LukeB101/Mega-Bit/Design History/Hardware/Prototype Modelling/README.md

Item | Description
--- | --- 
Acrylic 3D Final Prototype | Files for the laser cut case used in the final prototype design 
Production Product | Example injection moulded case for mass production
Prototype 1 8mm LEDs | Laser cut wooden prototype using 8mm LEDs
Prototype 2 10mm LEDs | Second prototype using updated 10mm LEDs
