LukeB101/Mega-Bit/Design History/Hardware/PCB/MEGABIT FINAL PCB/README.md

Revision 1 includes multiple redundant circuits including both HT16K33 and IS31FL3737 drivers.

Revision 2 is the final design for production using the IS31FL3737 and 3.3V buck devices.
