LukeB101/Mega-Bit/Project Management/Gantt Chart.pdf

## mega:bit Project Gantt Chart

Background Research | | | | Legend
Client Meeting | 1st meeting | 2nd meeting | 3rd meeting | General
Primary Research - Survey | | | | Hardware
Decide on Implementation | | | | Software
PCB Design | 1st revision | 2nd revision | 3rd revision | Deliverables
Software Design Method Selection
Supervisor Meeting
Software Implementation
PCB Building and Testing
Leaflet Design
Poster Design
Prototype Building and Testing
Client Demonstration | | 15th June
Deadlines
Leaflet | 9th June
Hackbooth | | 14th June
Documentation/Files | | | 27th June
Peer assessment | | | 27th June

week 6
02/06 - 08/06

week 7
09/06 - 15/06

week 8
16/06 - 22/06

week 9
23/06 - 29/06

week 1
28/04 - 04/05

week 2
05/05 - 11/05

week 3
12/05 - 18/05

week 4
19/05 - 25/05

week 5
26/05 - 1/06
