LukeB101/Mega-Bit/Deliverables/Hackbooth/Poster Illustrations/2nd Revision.png

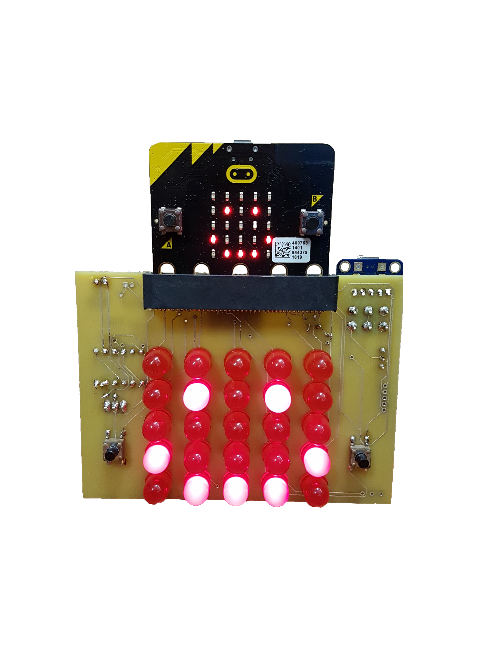
Deliverables/Hackbooth/Poster Illustrations/2nd Revision.png
