LukeB101/Mega-Bit/Deliverables/Hackbooth/Poster Illustrations/Megabit Schematic Diagram.png

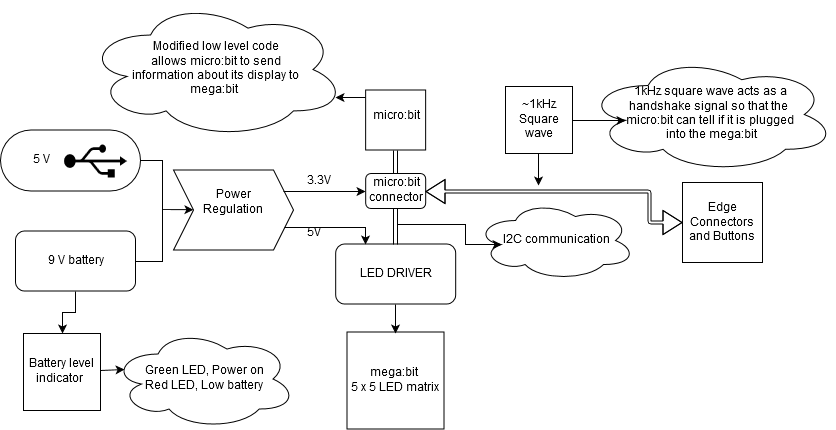
Deliverables/Hackbooth/Poster Illustrations/Megabit Schematic Diagram.png
