LukeB101/Mega-Bit/Deliverables/Leaflet/Leaflet Illustrations/Business Card Back.png

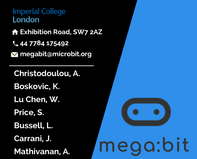
Deliverables/Leaflet/Leaflet Illustrations/Business Card Back.png
