LukeB101/Mega-Bit/Deliverables/Leaflet/Leaflet Illustrations/Business Card Front.png

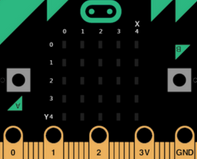
Deliverables/Leaflet/Leaflet Illustrations/Business Card Front.png
