LukeB101/Mega-Bit/Deliverables/Leaflet/Leaflet Illustrations/Megabit (blue).jpg

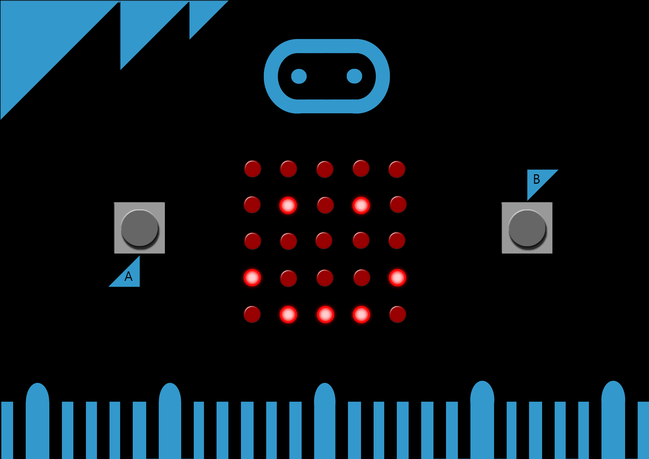
Deliverables/Leaflet/Leaflet Illustrations/Megabit (blue).jpg
