LukeB101/Mega-Bit/Deliverables/Leaflet/Leaflet Illustrations/Megabit Final Design.jpg

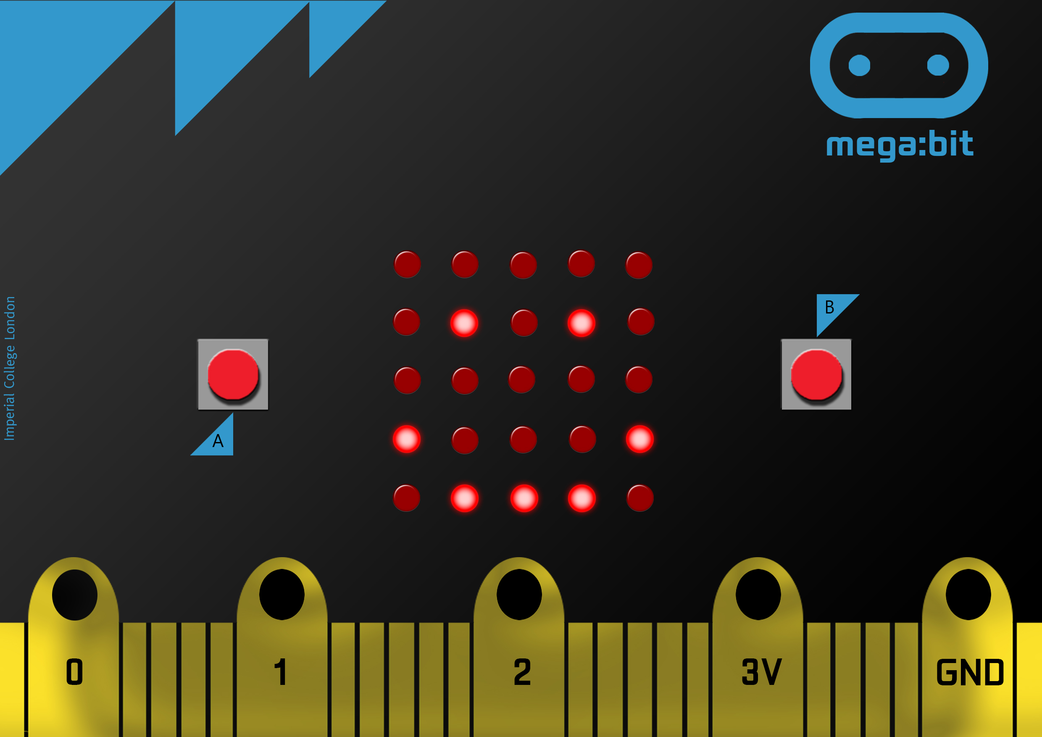
Deliverables/Leaflet/Leaflet Illustrations/Megabit Final Design.jpg
