LukeB101/Mega-Bit/Deliverables/Leaflet/Leaflet Illustrations/Megabit with Slot.jpg

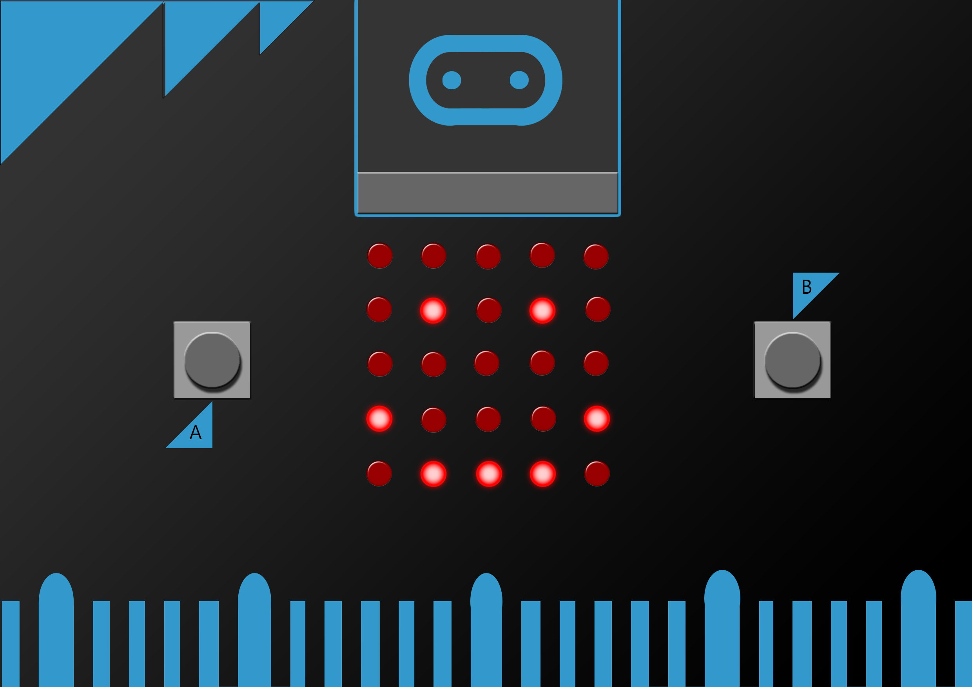
Deliverables/Leaflet/Leaflet Illustrations/Megabit with Slot.jpg
