LukeB101/Mega-Bit/Deliverables/Leaflet/Leaflet Illustrations/Piechart.png

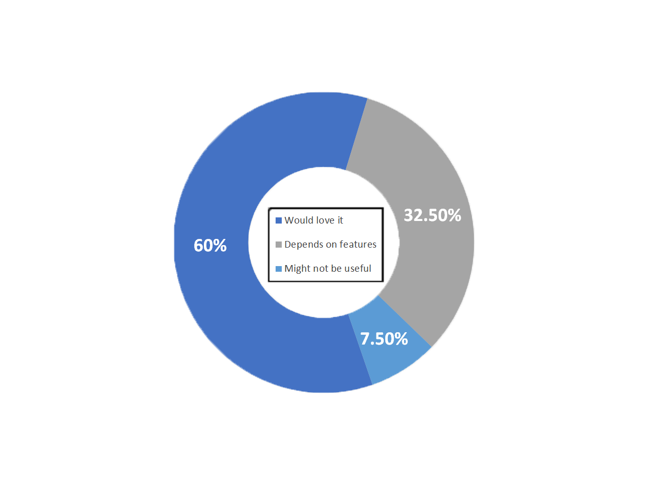
Deliverables/Leaflet/Leaflet Illustrations/Piechart.png
