LukeB101/Mega-Bit/Design History/Hardware/Prototype Modelling/Production Product/Final Design/render of case with PCB.PNG

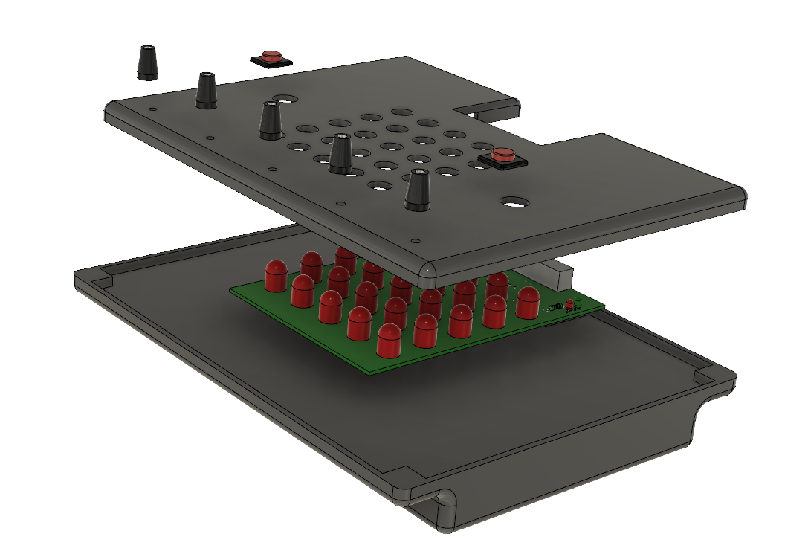
Design History/Hardware/Prototype Modelling/Production Product/Final Design/render of case with PCB.PNG
