LukeB101/Mega-Bit/Design History/Hardware/Prototype Modelling/Production Product/Final Design/render of MegaBit.PNG

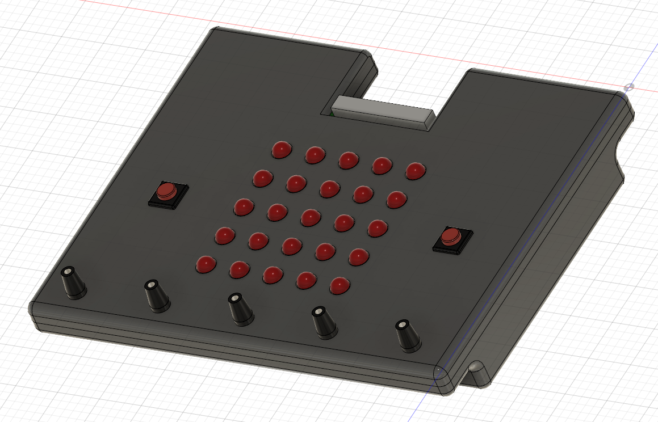
Design History/Hardware/Prototype Modelling/Production Product/Final Design/render of MegaBit.PNG
