LukeB101/Mega-Bit/Design History/Hardware/Prototype Modelling/Production Product/Production Quote Files/back.PNG

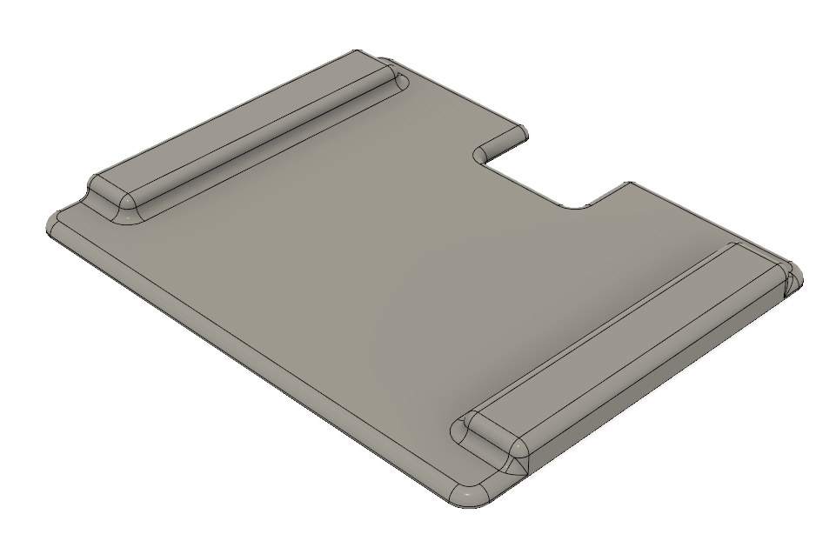
Design History/Hardware/Prototype Modelling/Production Product/Production Quote Files/back.PNG
