LukeB101/Mega-Bit/Design History/Hardware/Prototype Modelling/Prototype 1 8mm LEDs/8mm LED MegaBit.png

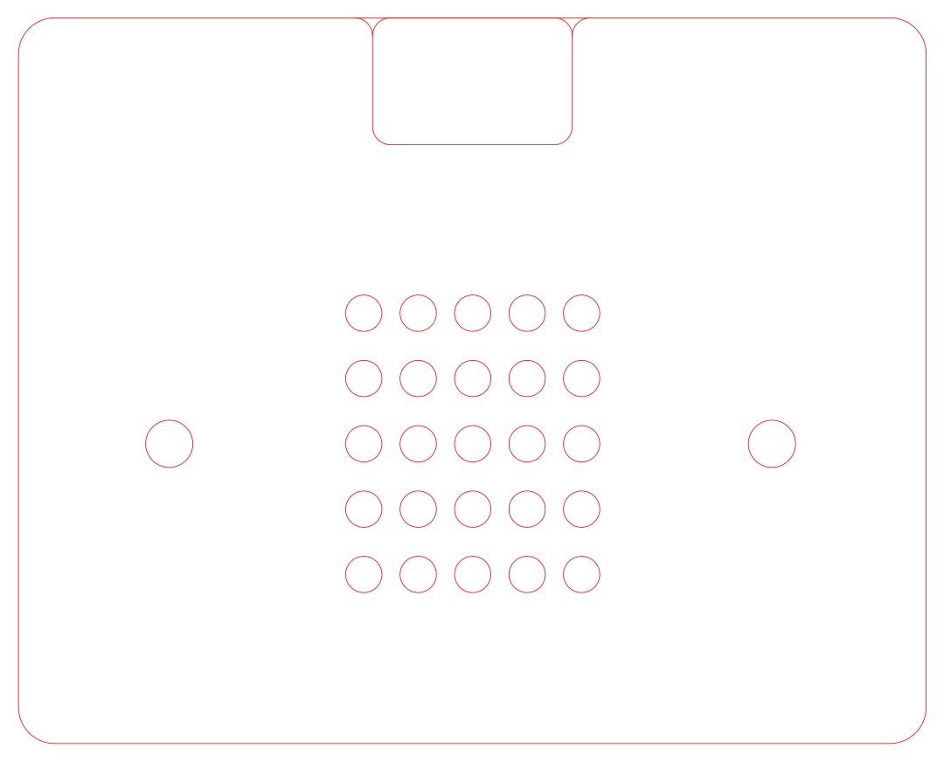
Design History/Hardware/Prototype Modelling/Prototype 1 8mm LEDs/8mm LED MegaBit.png
