LukeB101/Mega-Bit/Design History/Hardware/Prototype Modelling/Prototype 2 10mm LEDs/10mm LED MegaBit.png

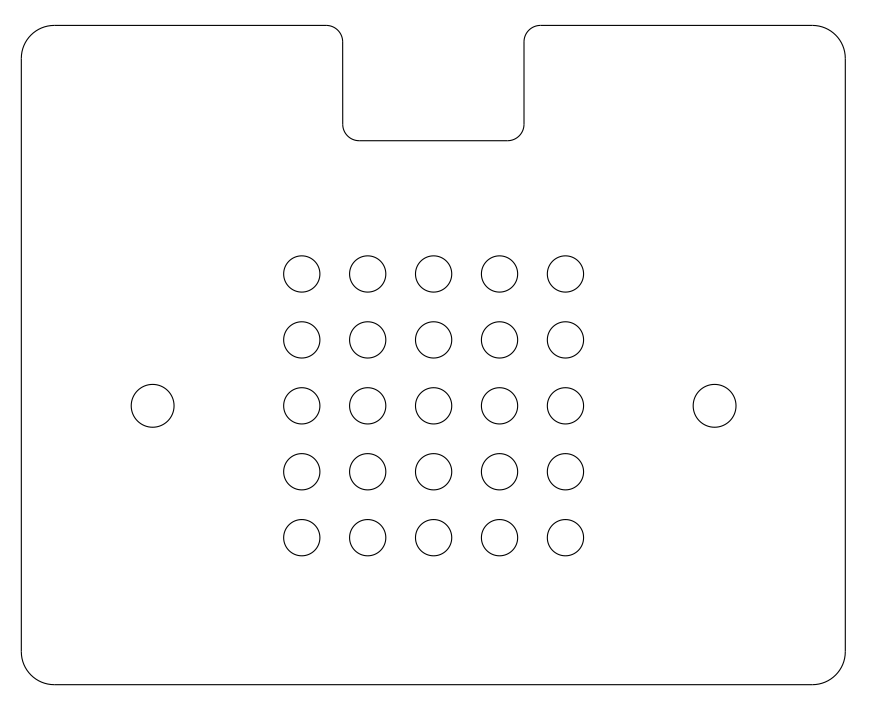
Design History/Hardware/Prototype Modelling/Prototype 2 10mm LEDs/10mm LED MegaBit.png
