LukeB101/Mega-Bit/Design History/Hardware/Prototype Modelling/Prototype 2 10mm LEDs/front dimensions.PNG

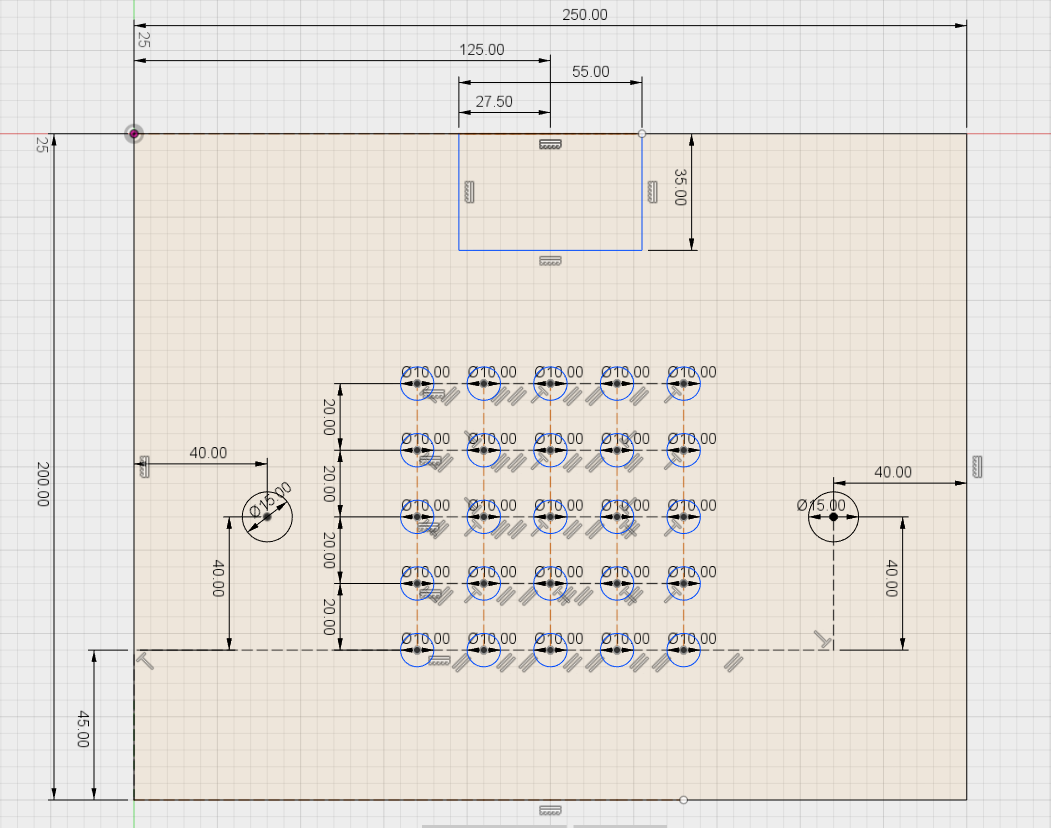
Design History/Hardware/Prototype Modelling/Prototype 2 10mm LEDs/front dimensions.PNG
