LukeB101/Mega-Bit/Final Product Design/CAD Files/back.PNG

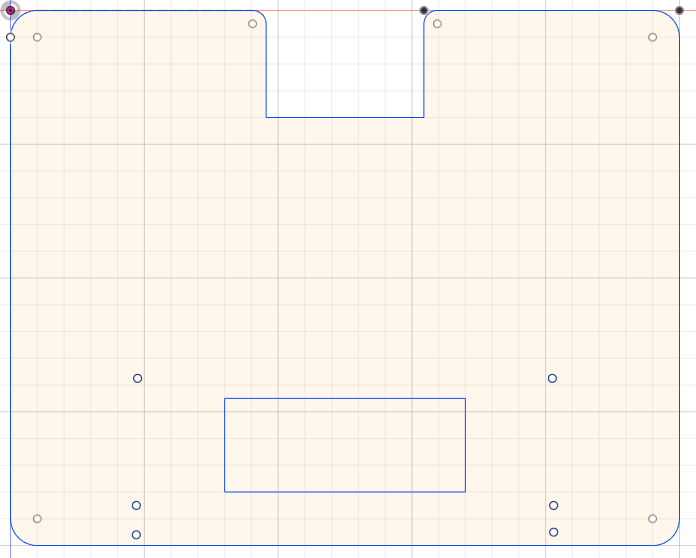
Final Product Design/CAD Files/back.PNG
