LukeB101/Mega-Bit/Final Product Design/CAD Files/front acrylic cover.PNG

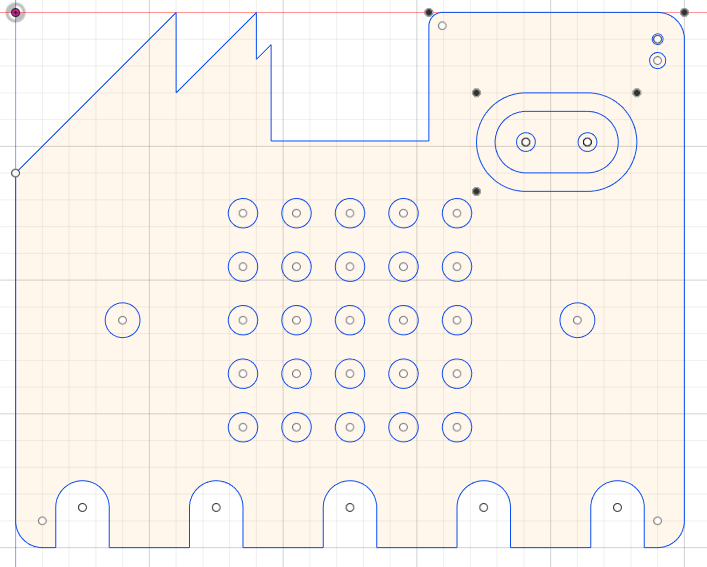
Final Product Design/CAD Files/front acrylic cover.PNG
