LukeB101/Mega-Bit/Final Product Design/CAD Files/front painted layer.PNG

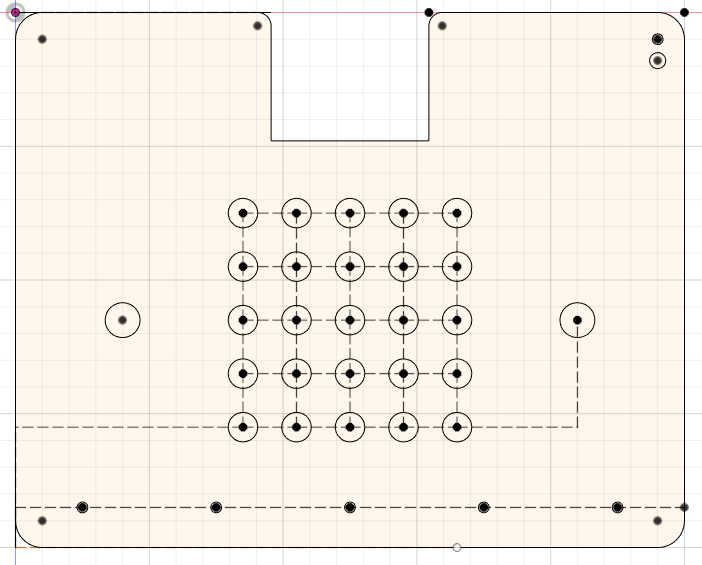
Final Product Design/CAD Files/front painted layer.PNG
