LukeB101/Mega-Bit/Final Product Design/CAD Files/sides.PNG

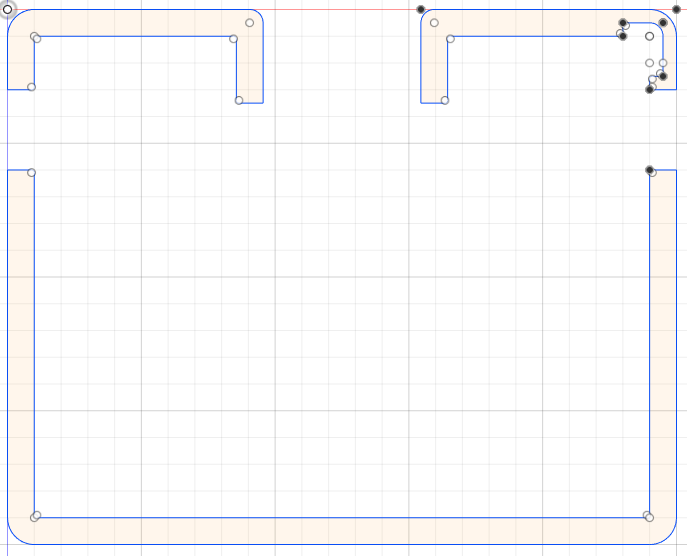
Final Product Design/CAD Files/sides.PNG
