LukeB101/Mega-Bit/Final Product Design/CAD Files/stand.PNG

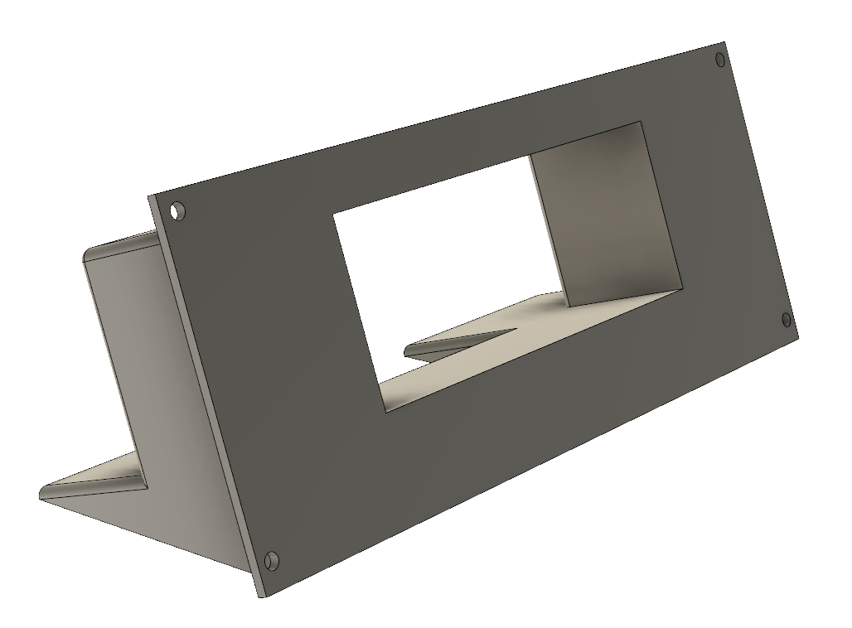
Final Product Design/CAD Files/stand.PNG
