LukeB101/Mega-Bit/pictures/Final prototype back view.jpg

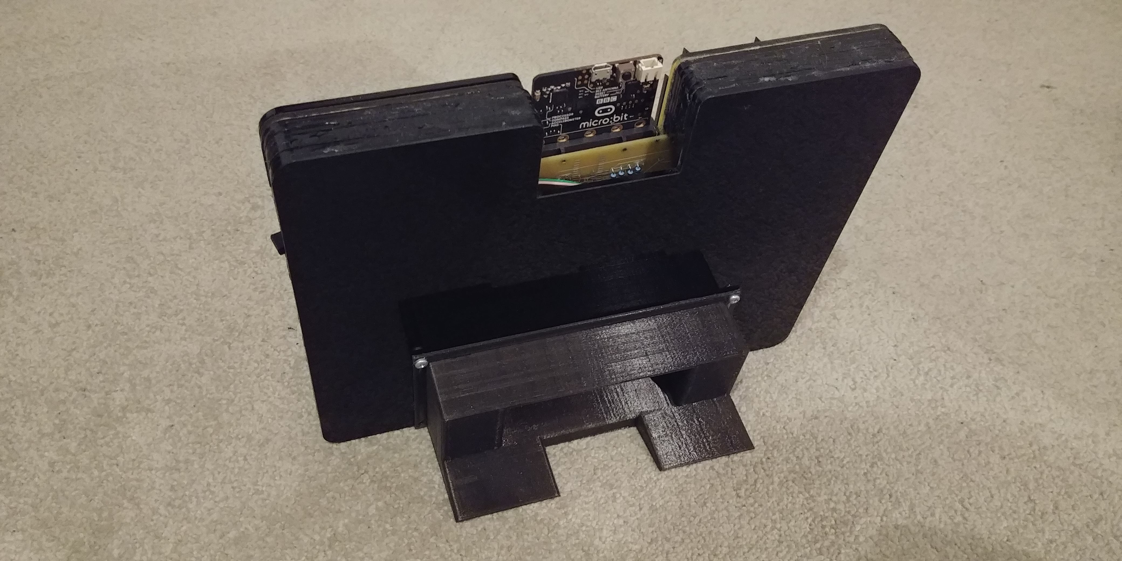
pictures/Final prototype back view.jpg
