LukeB101/Mega-Bit/pictures/Final prototype front view.jpg

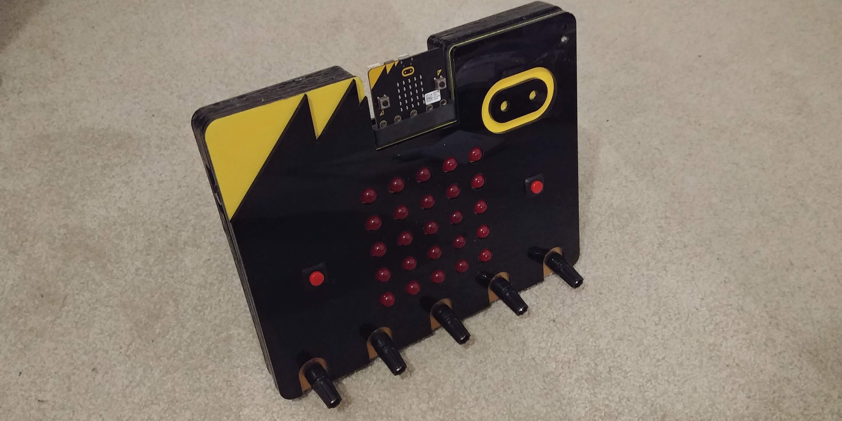
pictures/Final prototype front view.jpg
