LukeB101/Mega-Bit/Design History/Manufacturing/Plastic Case Supplier Quotes/Plastic Mold Quote - China Plastic.pdf

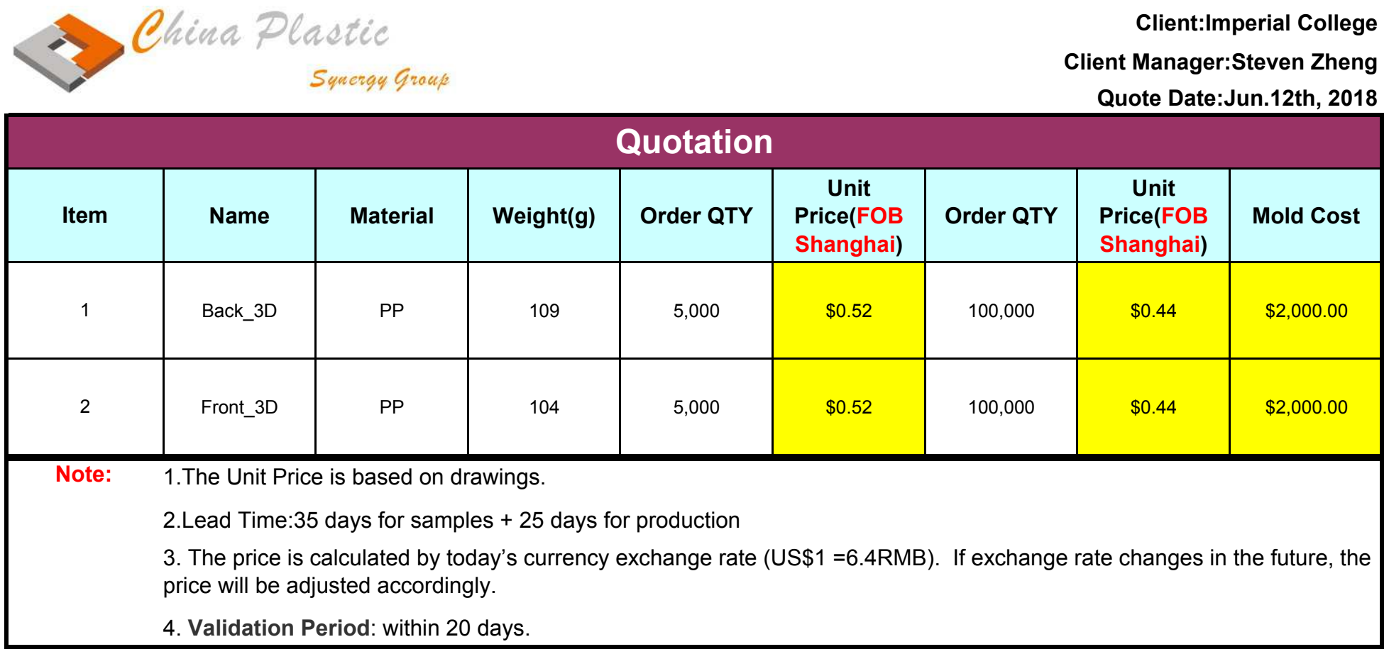
[picture p42: figure]
Client:Imperial College; Client Manager:Steven Zheng; Quote Date:Jun.12th, 2018; Item; Name; Material; Weight(g); Order QTY; Unit Price(FOB Shanghai); Mold Cost; Back_3D; Front_3D; Note:; 4. Validation Period: within 20 days.; 1.The Unit Price is based on drawings.; Quotation; price will be adjusted accordingly.

2.Lead Time:35 days for samples + 25 days for production
3. The price is calculated by today’s currency exchange rate (US$1 =6.4RMB). If exchange rate changes in the future, the
