LukeB101/Mega-Bit/Design History/Components/Microbit Breakout Board/Supplier Order.JPG

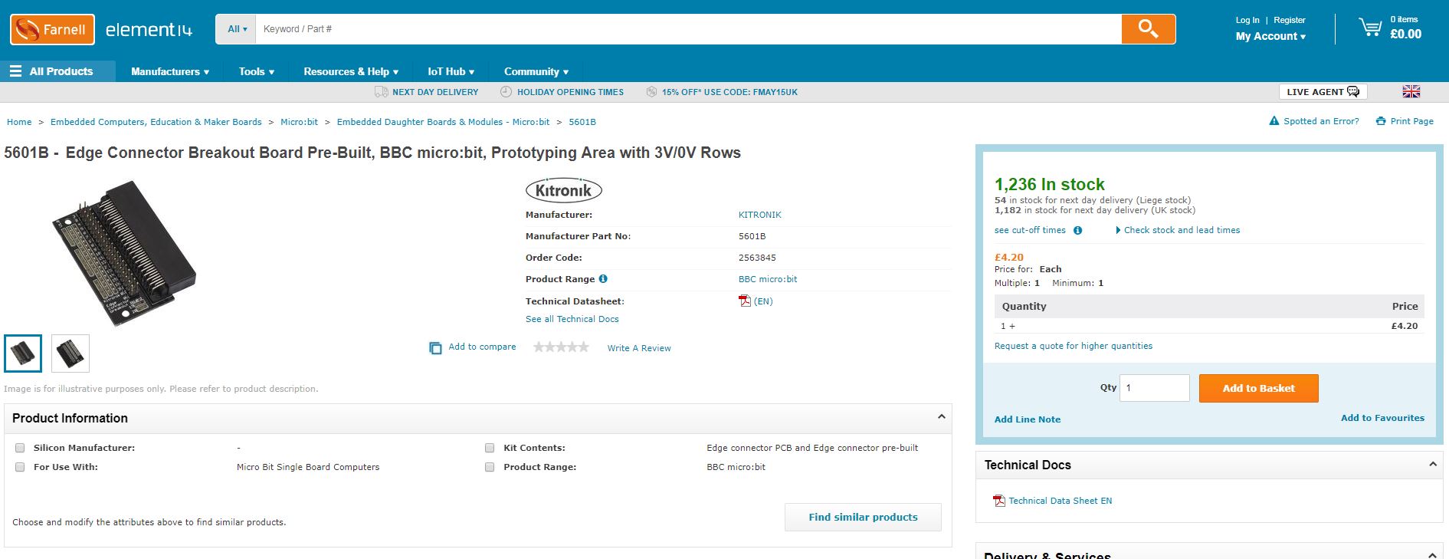
Design History/Components/Microbit Breakout Board/Supplier Order.JPG
