LukeB101/Mega-Bit/Design History/End Product Testing/Pictures/3V3 + 5V.png

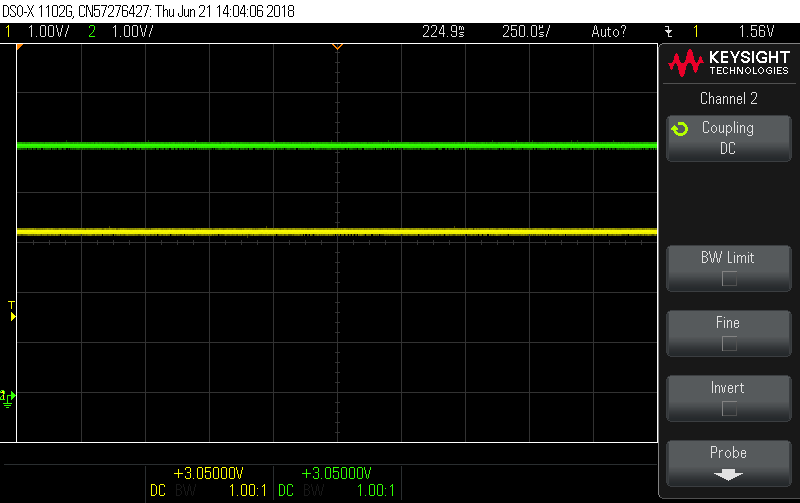
Design History/End Product Testing/Pictures/3V3 + 5V.png
