LukeB101/Mega-Bit/Design History/End Product Testing/Pictures/Distance test.jpg

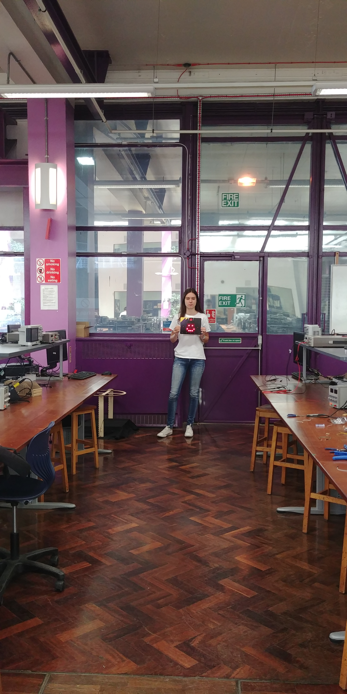
Design History/End Product Testing/Pictures/Distance test.jpg
