LukeB101/Mega-Bit/Design History/End Product Testing/Pictures/I2C example.png

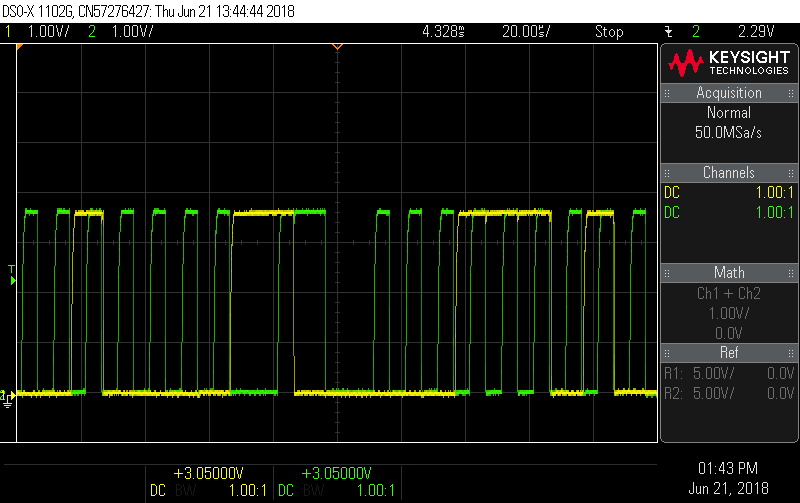
Design History/End Product Testing/Pictures/I2C example.png
