LukeB101/Mega-Bit/Design History/End Product Testing/Pictures/Single TX.png

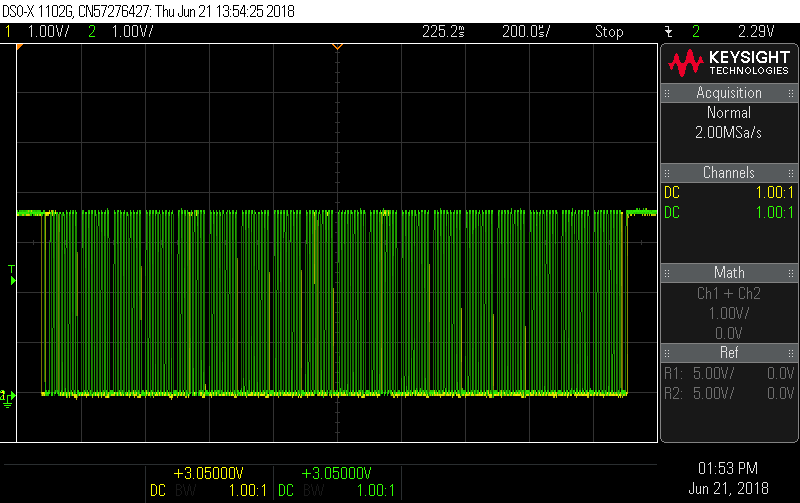
Design History/End Product Testing/Pictures/Single TX.png
