LukeB101/Mega-Bit/Design History/End Product Testing/Pictures/Startup Comms.png

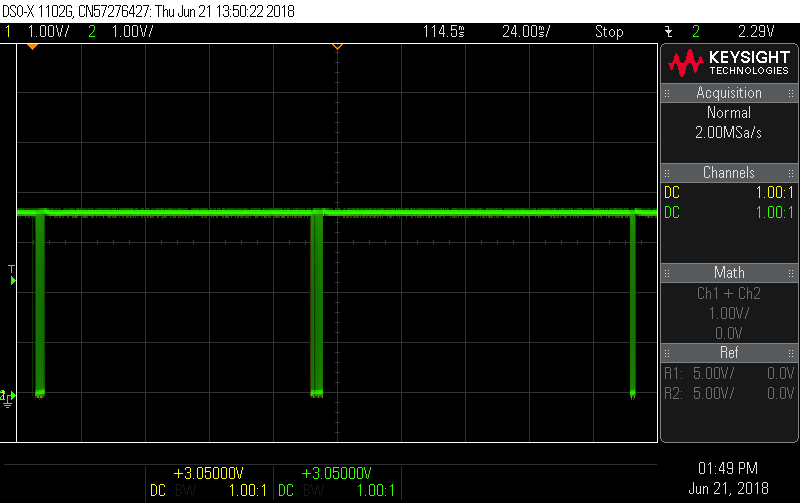
Design History/End Product Testing/Pictures/Startup Comms.png
