LukeB101/Mega-Bit/Final Product Design/PCB/rev2 (incomplete)/MEGABIT.PDF

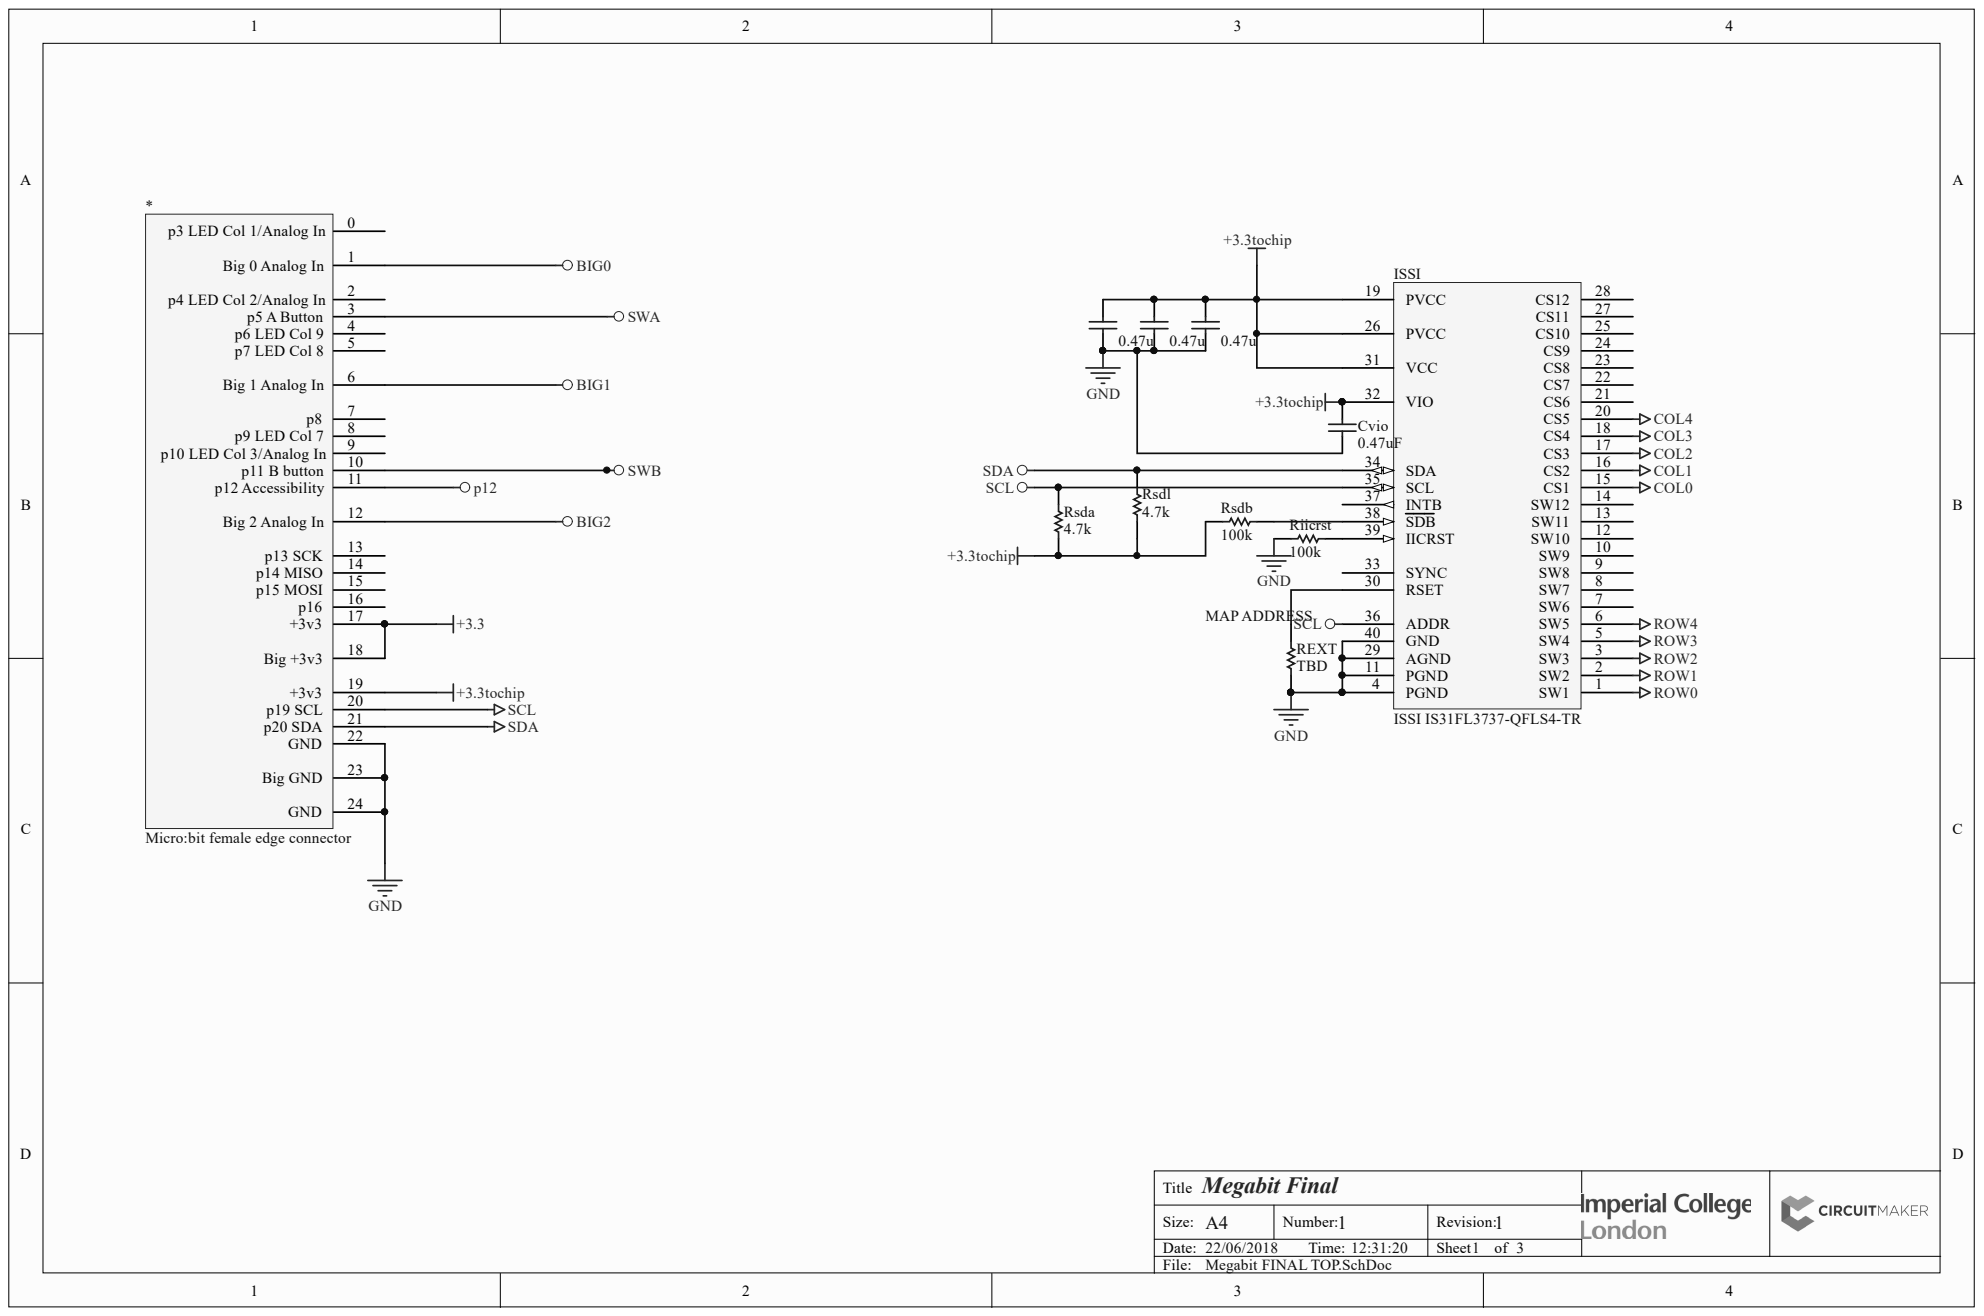
[picture p93: page 1]
t FIN; 1 PGND; ISSI IS3; 3 SCK 4 MISO 5 MOSI; 9 SCL 0 SD; t female ed; PIRsdb02 PIRsdl02; PIRiicrst01 PIISSI039; PIISSI034 PIRsdl01

T i t l e Mega bit Fina l

Size: A4 | N umber: 1 | Rev i s i o n : 1
Date: / / T ime: : : | | Sheet o f


Title Megabit LED Matrix

Size: A4 | Number: 2 | Revision: 1
22/06/2018 Time: 12:31:20 | | Sheet of

tery i; PIU103; PIDlow02 PIU101

T i t l e Mega bit Battery Indicato r

Size: A4 | N umber: 3 | Rev i s i o n : 1

/ / T ime: : : | | Sheet o f

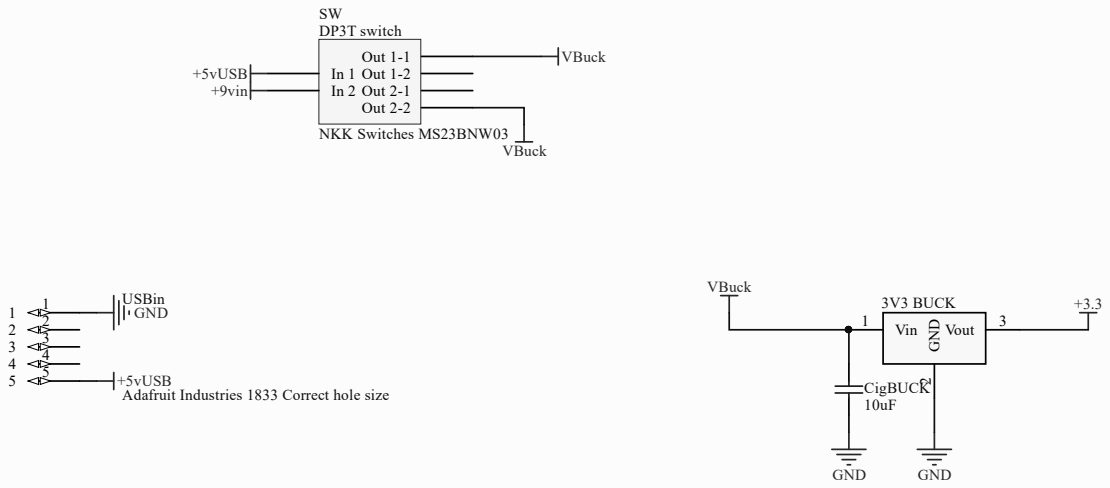
[picture p94: page 4]
Vin 1; GND 2 Vout 3; 3V3 BUCK; Out 1-1 Out 1-2 Out 2-1; DP3T switch; Out 2-2; NKK Switches MS23BNW03; PI3V3 BUCK01; PI3V3 BUCK02; PI3V3 BUCK03; CO3V3 BUCK; PICigBUCK02 COCigBUCK

+5vUSB
Adafruit Industries 1833 Correct hole size

Title Megabit Final Power

Size: A4 | Number: 4 | Revision: 1

TRIG 2; RST 4; THR 6; GND; Res1 C555

f= 1/(1.4RC), datasheet reccomends minimal C and large R

Title Megabit Final Handshake Circuitry

Size: A4 | Number: 5 | Revision: 1
