LukeB101/Mega-Bit/Design History/Hardware/PCB/PCB 3rd revision/MEGABIT.PDF

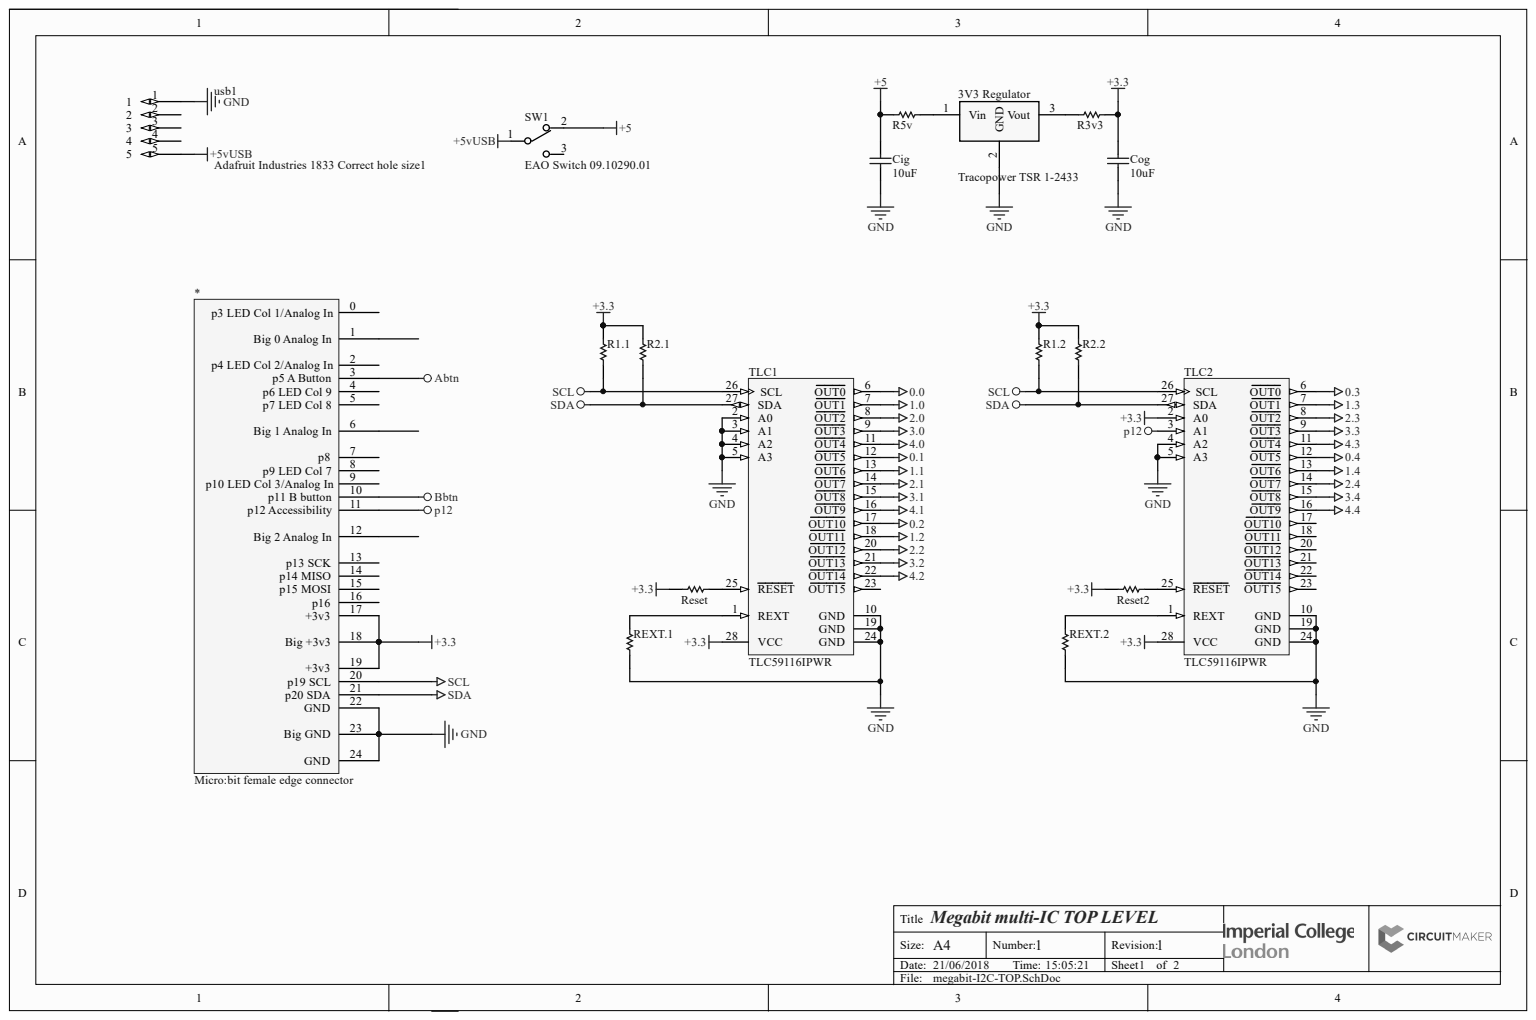
[picture p95: page 1]
EAO Switch 09.10290.01; REXT 1; RESET 25; SCL 26 SDA 27; VCC 28; 4.4 GND; GND; Reset2 +3.3; +3.3 Reset; p3 LED Col 1/Analog In; Big 0 Analog In; p4 LED Col 2/Analog In; p5 A Button; p6 LED Col 9; p7 LED Col 8; Big 1 Analog In; p9 LED Col 7; p10 LED Col 3/Analog In; p11 B button; p12 Accessibility; Big 2 Analog In; p13 SCK; p14 MISO; p15 MOSI; Big +3v3; p19 SCL; p20 SDA; Big GND; Vin 1; GND 2 Vout 3; 3V3 Regulator; Tracopower TSR 1-2433

+5vUSB
Adafruit Industries 1833 Correct hole size1

Micro:bit female edge connector

Title Megabit multi-IC TOP LEVEL

Size: A4 | Number: 1 | Revision: 1
Date: 21/06/2018 Time: 15:05:21 | | Sheet 1 of 2

megabit-I2C-TOP.SchDoc

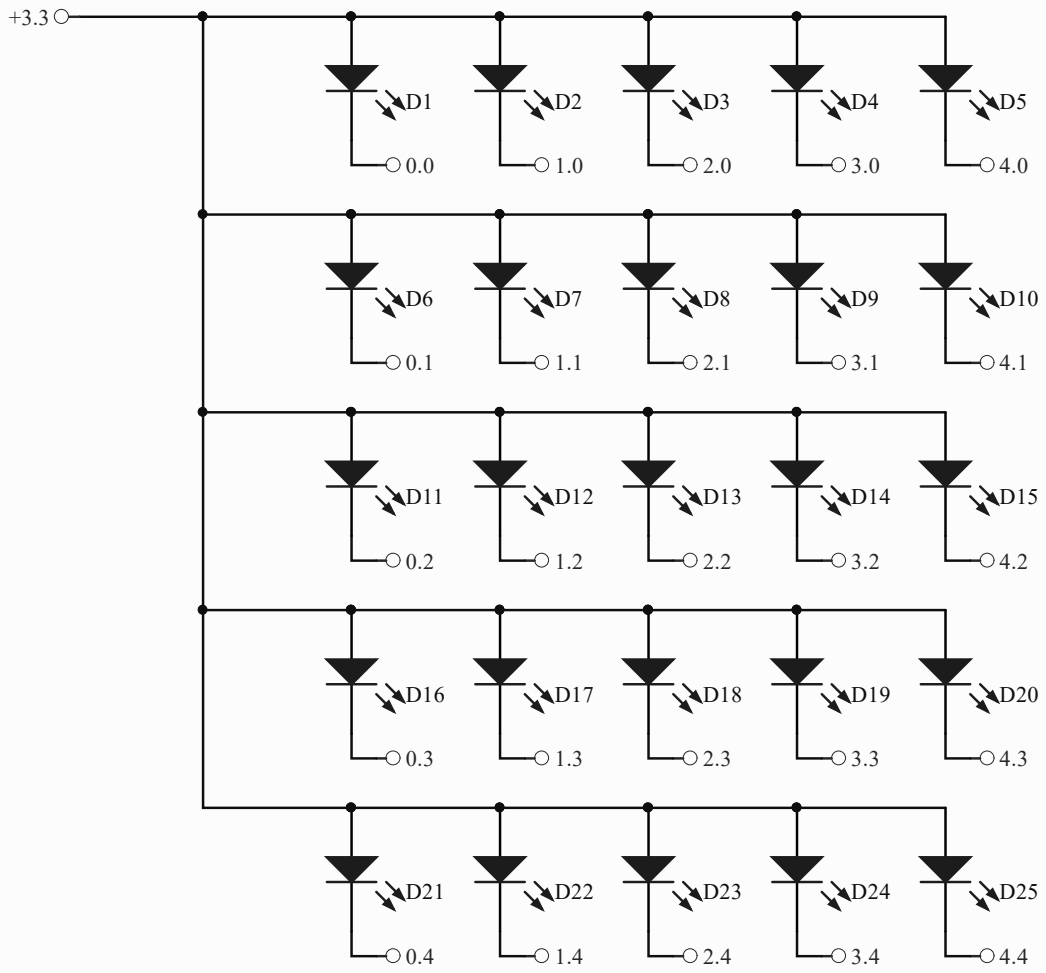
[picture p96: page 2]

Title Megabit LED Matrix

Size: A4 | Number: 1 | Revision: 1
Date: 21/06/2018 Time: 15:05:22 | | Sheet 2 of 2

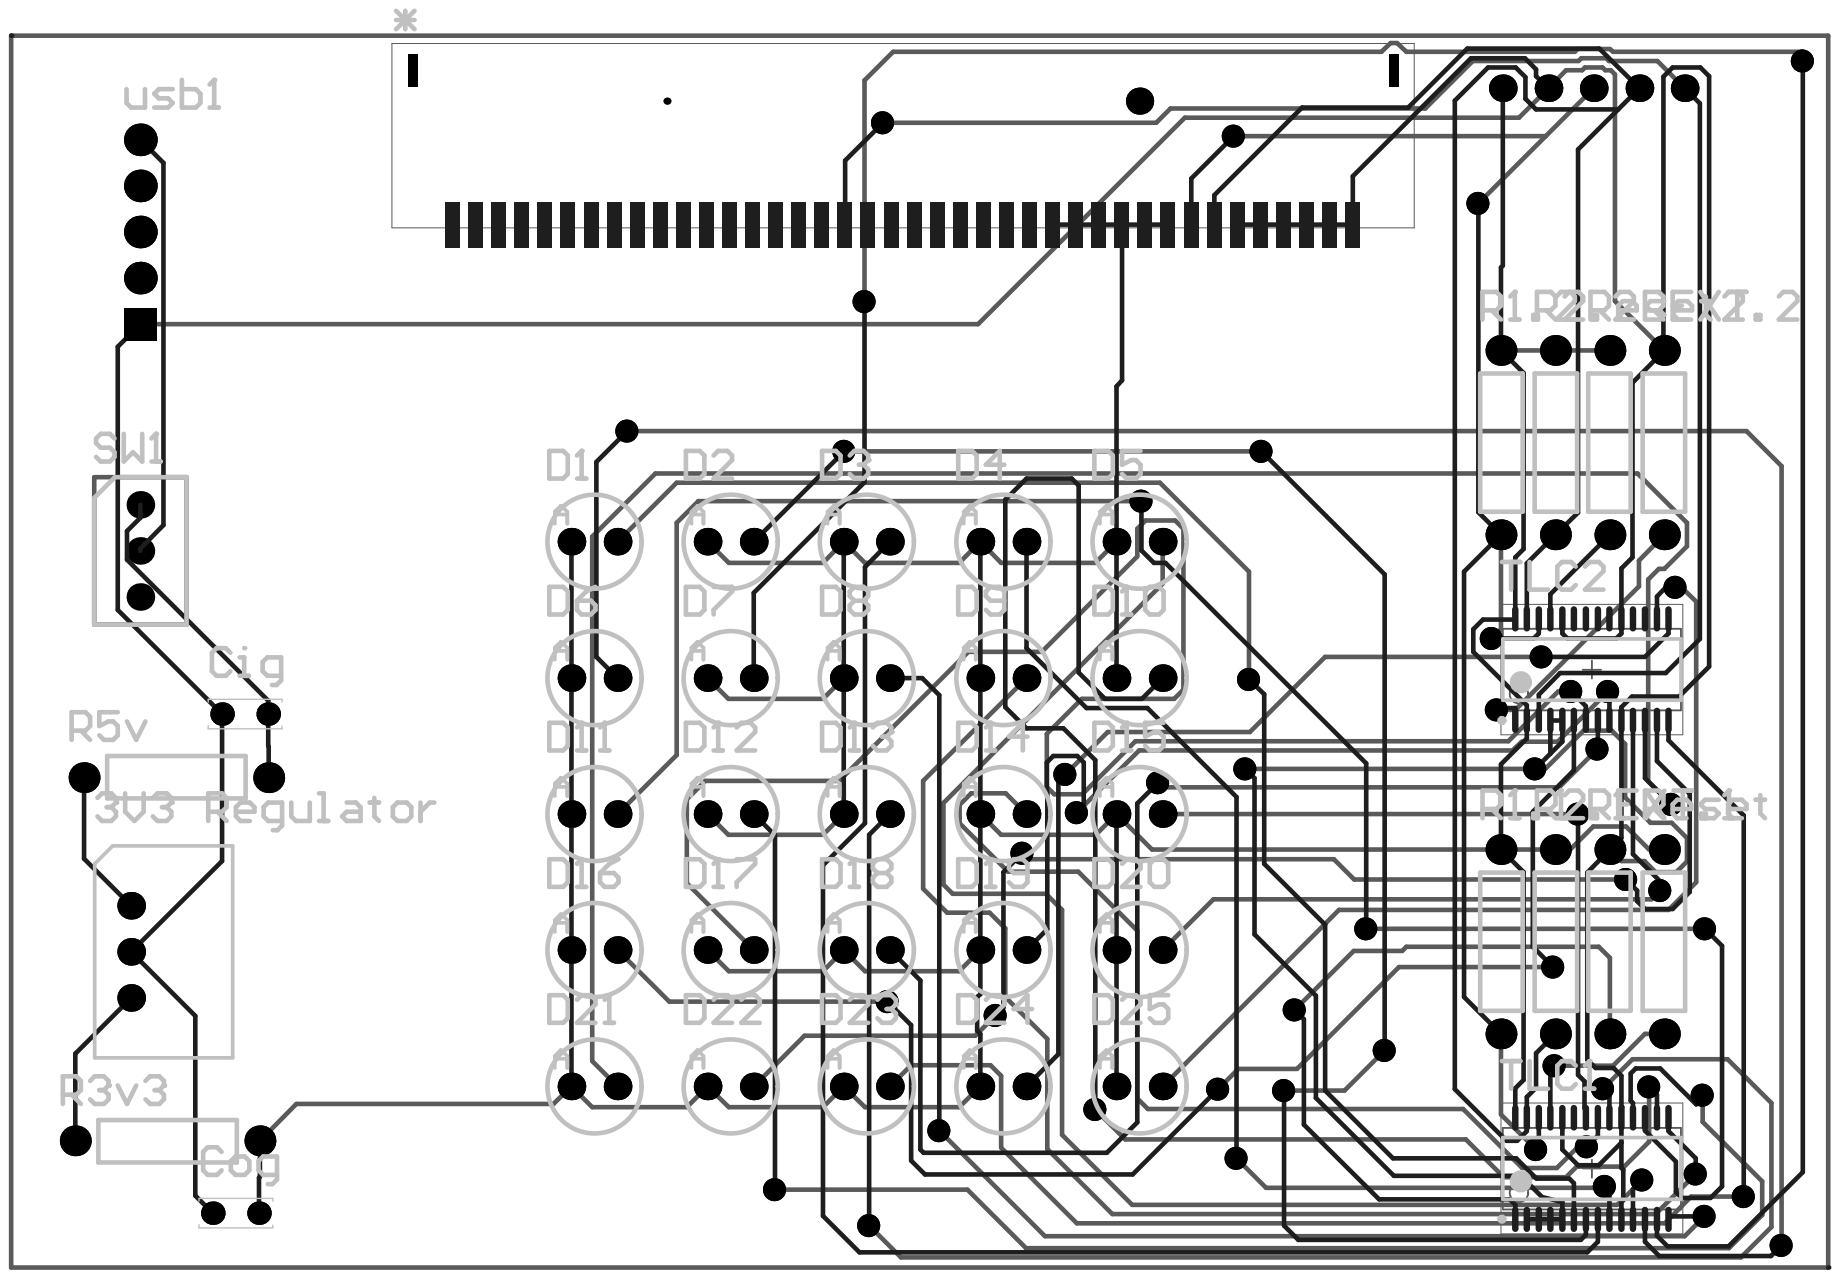
[picture p97: page 3]

# Board S
