LukeB101/Mega-Bit/Design History/Hardware/PCB/PCB 2nd revision/MEGABIT rev.2.PDF

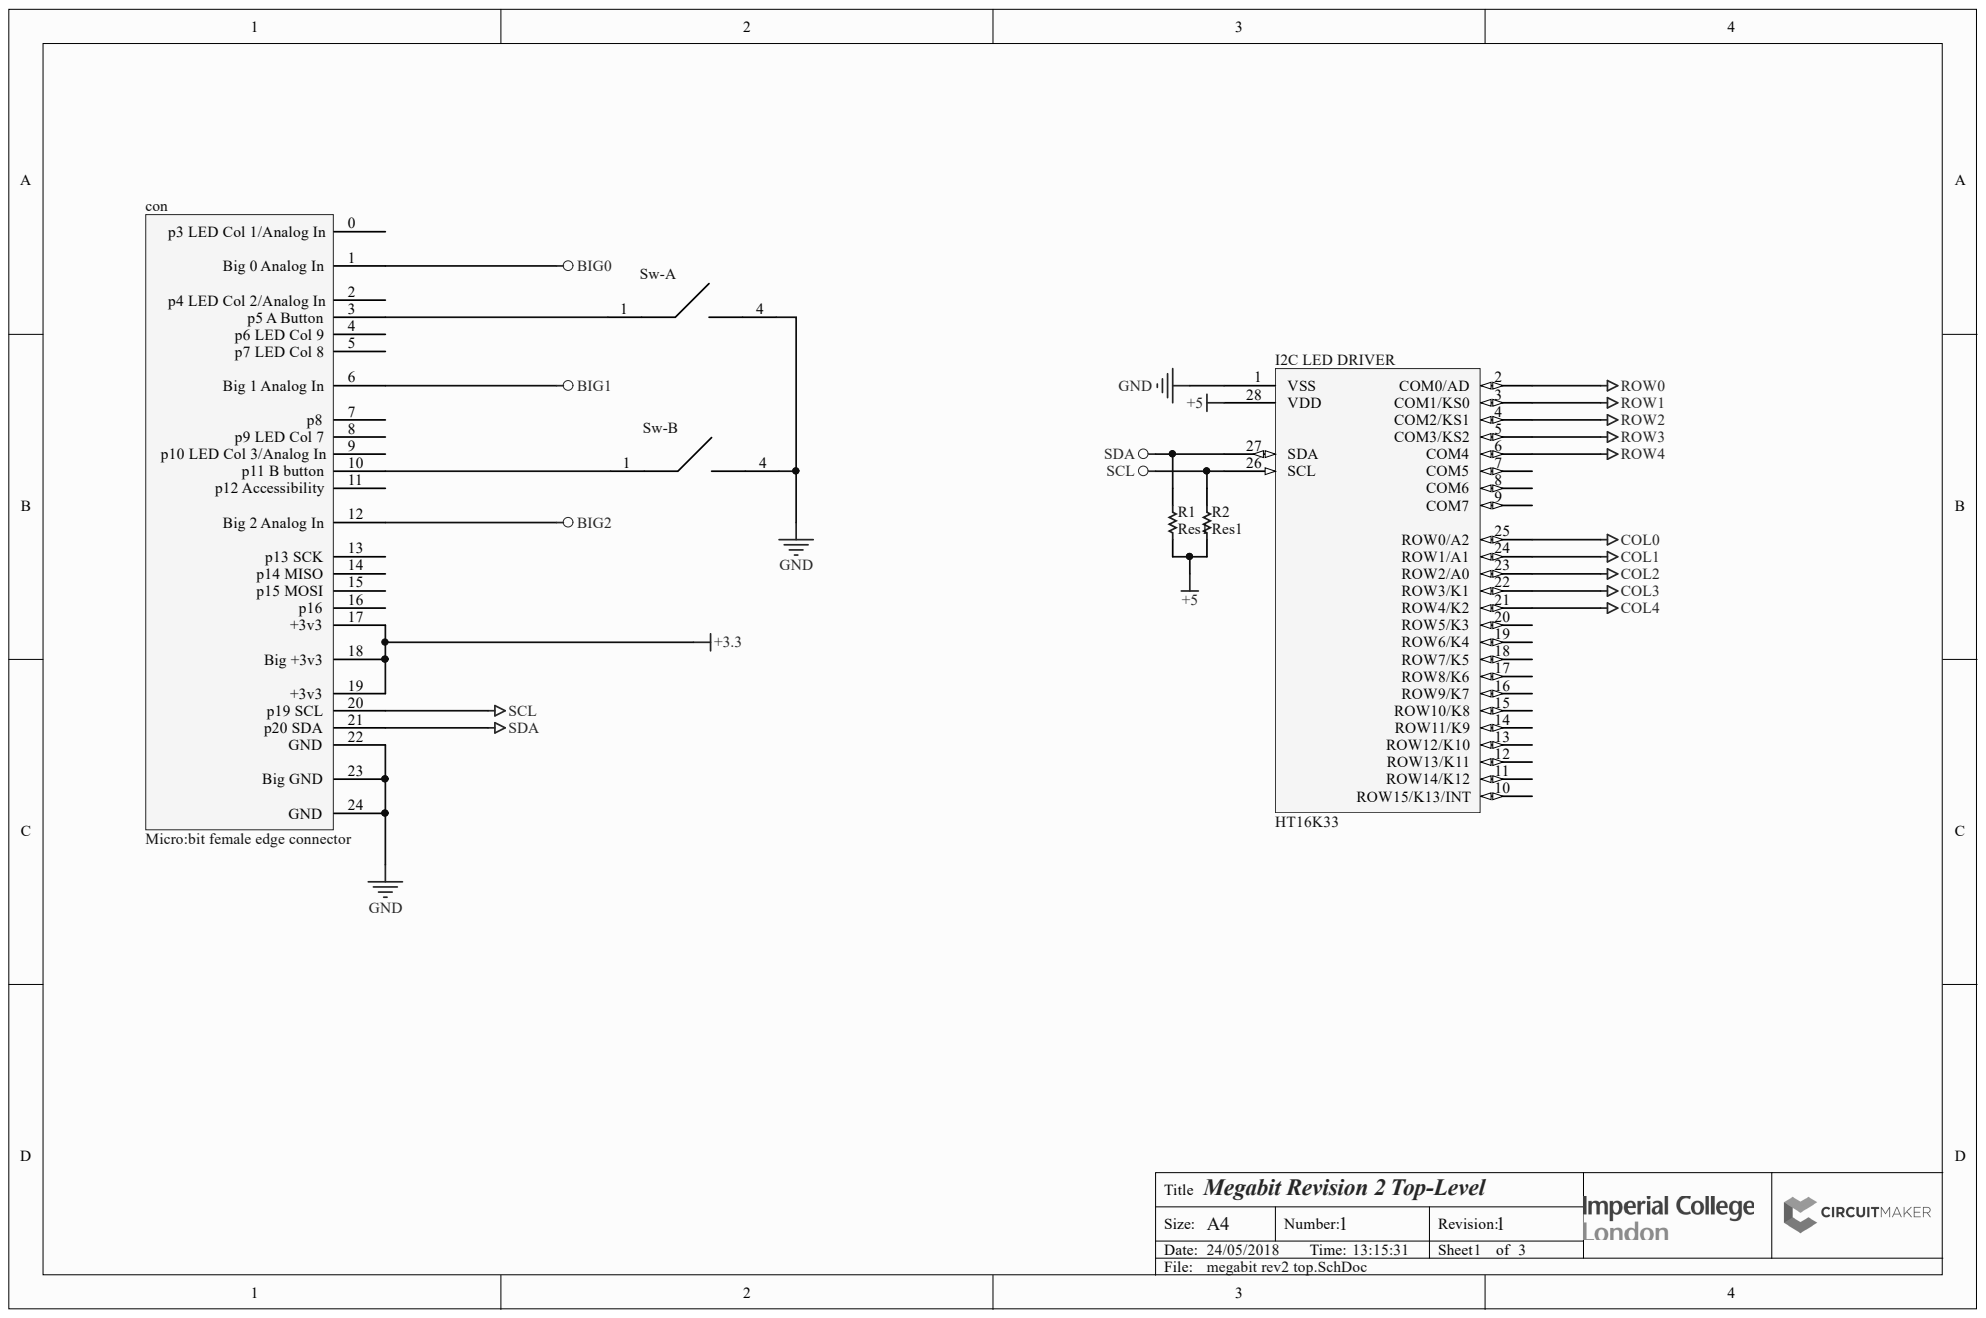
[picture p98: page 1]
t rev; 0 ROW14/K12; 11 ROW13/K11; 12 ROW12/K10; 13 ROW11/K9; 14 ROW10/K8; 15 ROW9/K7; 16 ROW8/K6; 17 ROW7/K5; 18 ROW6/K4; 19 ROW5/K3; 20 ROW4/K2; 21 ROW3/K1; 22 ROW2/A0; 23 ROW1/A1; 24 ROW0/A2; D DRIV; 3 SCK 4 MISO 5 MOSI; 9 SCL 0 SD; t female ed; PII2C LED DRIVER01; PII2C LED DRIVER02; PII2C LED DRIVER03; PII2C LED DRIVER04 PII2C LED DRIVER05 PII2C LED DRIVER06; PII2C LED DRIVER07; PII2C LED DRIVER08 PII2C LED DRIVER09; PII2C LED DRIVER010; PII2C LED DRIVER011; PII2C LED DRIVER012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

Mega T i t l e

bit Revision 2 Top-Level 1

A4 Size: | N umber: | 1 Rev i s i o n :
Date: / / T ime: : : | | Sheet o f

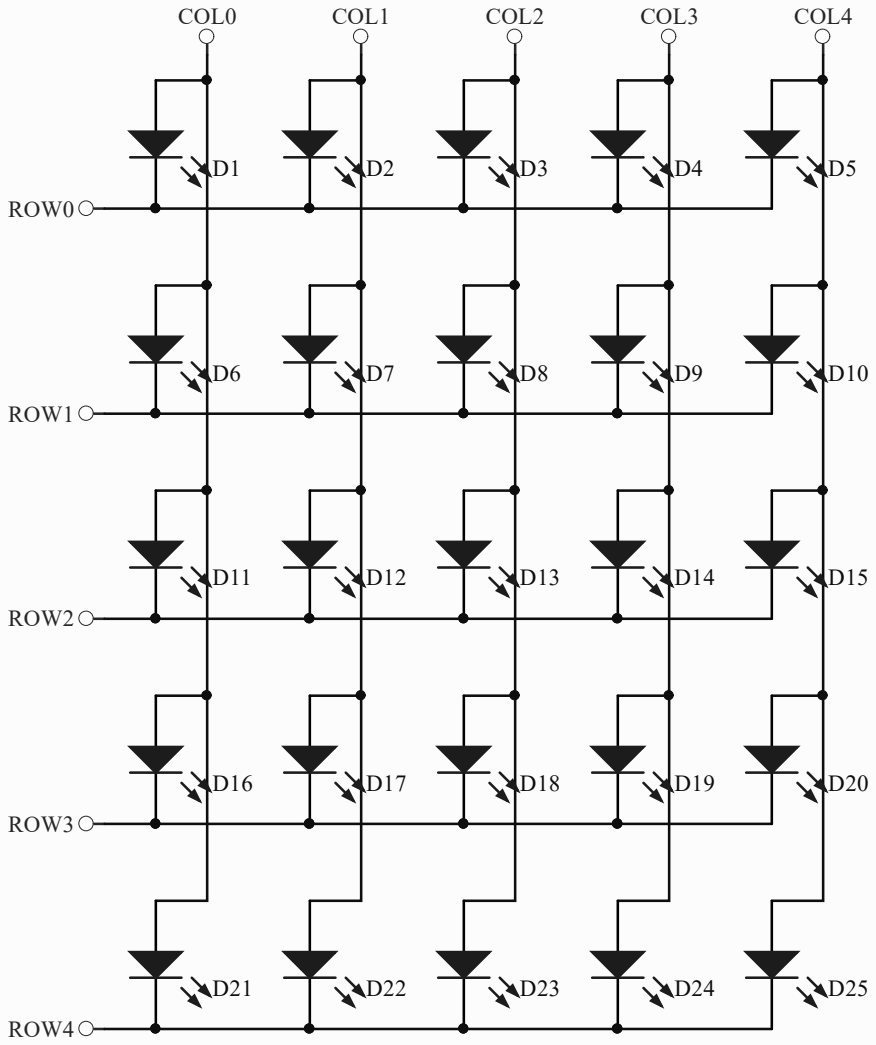
[picture p99: page 2]

Megabit LED Matrix Title

A4 Size: | 2 Number: | 1 Revision:
24/05/2018 Time: 13:15:31 | | Sheet 2 of 3

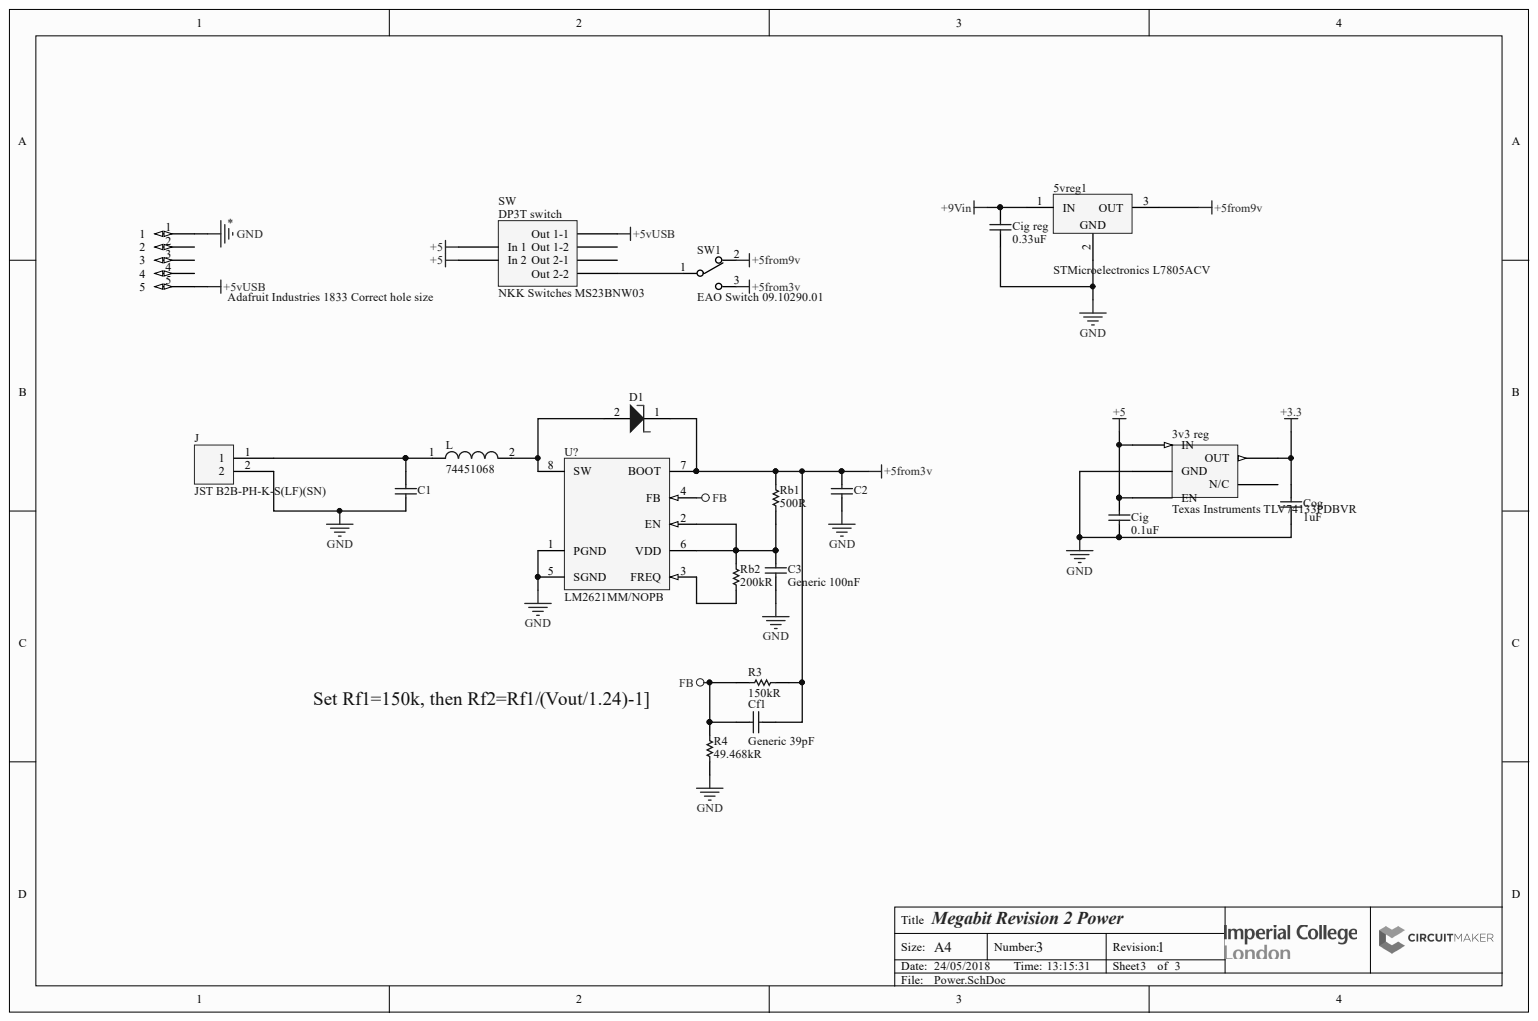
[picture p100: page 3]
PGND 1; SGND 5; BOOT; Generic 100nF; Generic 39pF; EAO Switch 09.10290.01; Cig reg; 3v3 reg; Texas Instruments TLV74133PDBVR; Out 1-1 Out 1-2 Out 2-1; DP3T switch; Out 2-2; NKK Switches MS23BNW03; 2 OUT 3; STMicroelectronics L7805ACV

+5vUSB
Adafruit Industries 1833 Correct hole size

JST B2B-PH-K-S(LF)(SN)

Set Rf1=150k, then Rf2=Rf1/(Vout/1.24)-1]

Megabit Revision 2 Power Title

A4 Size: | 3 Number: | 1 Revision:
24/05/2018 Time: 13:15:31 | | Sheet 3 of 3

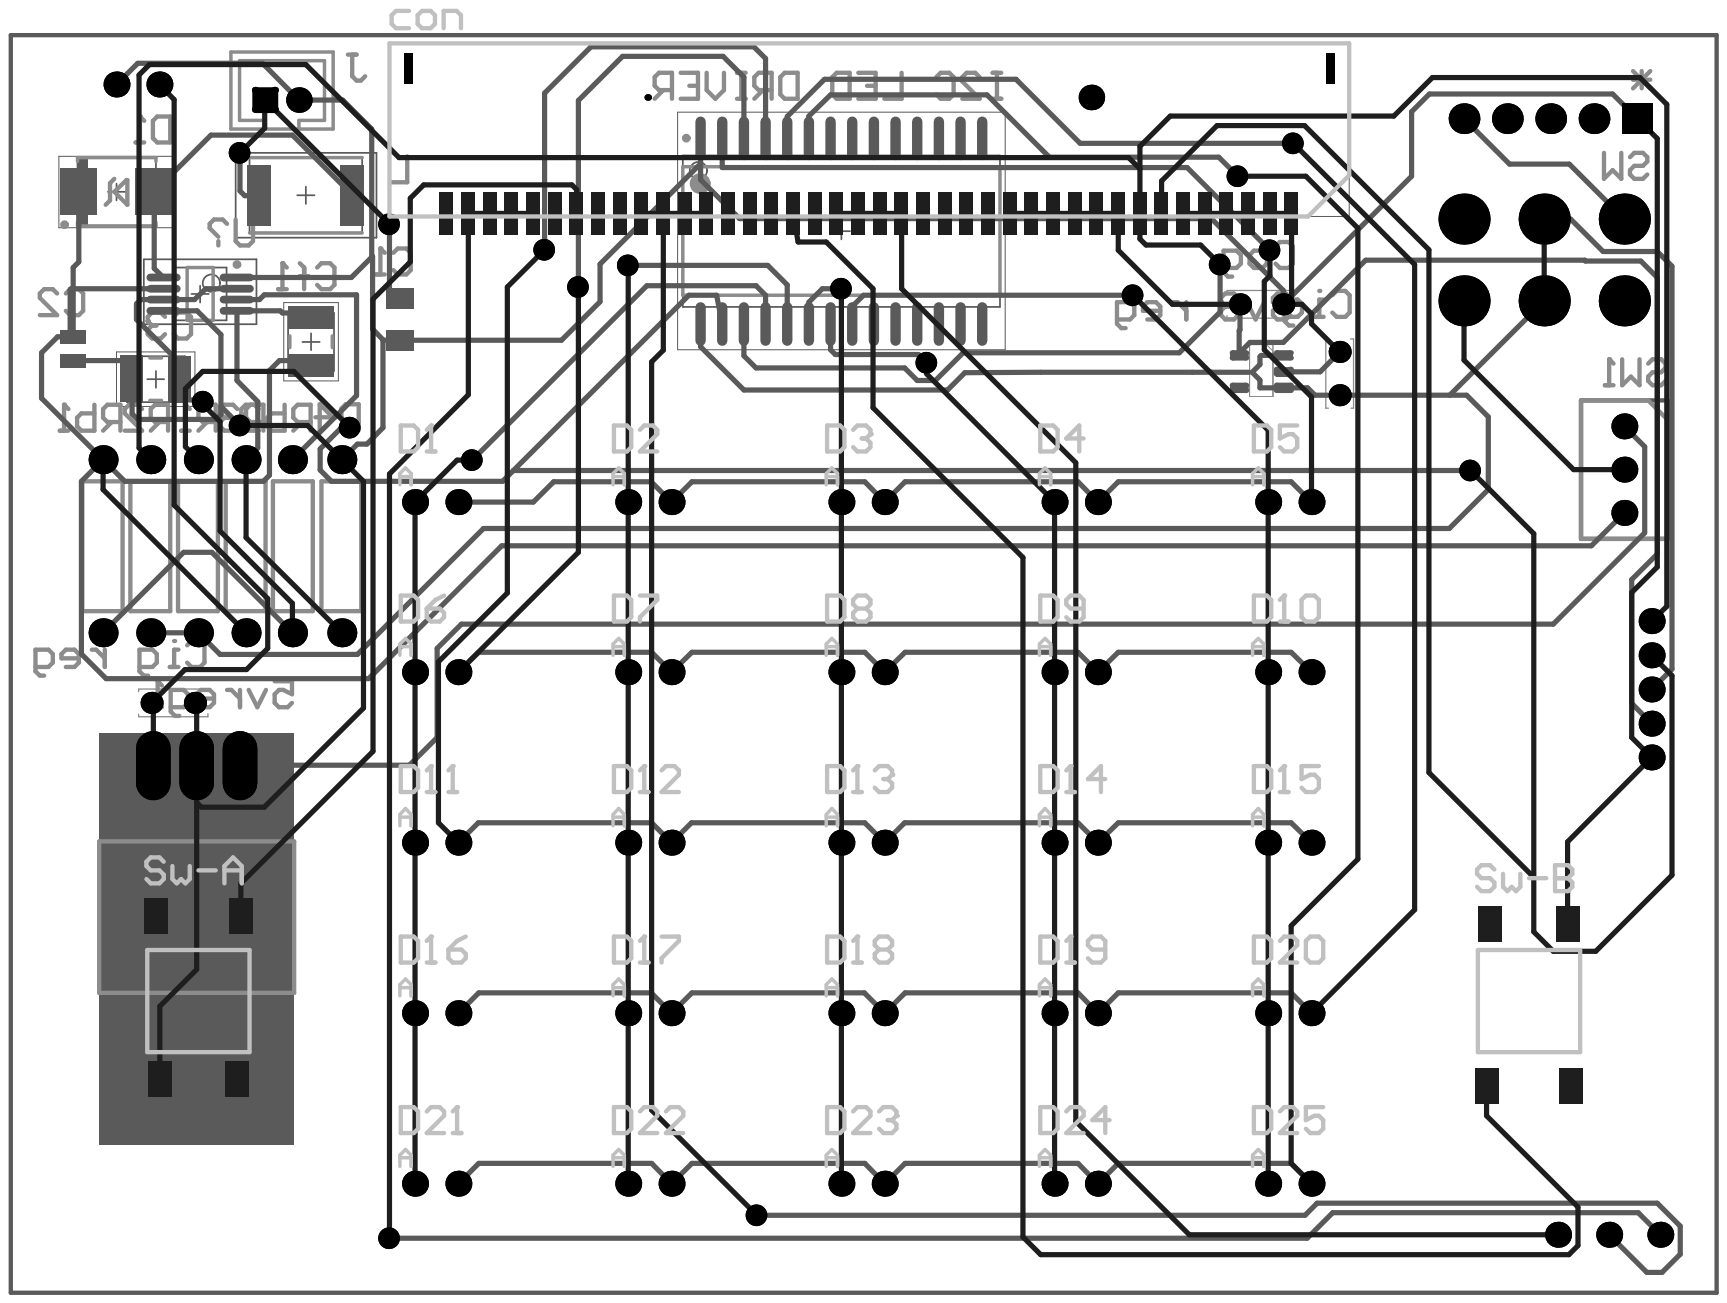
[picture p101: page 4]

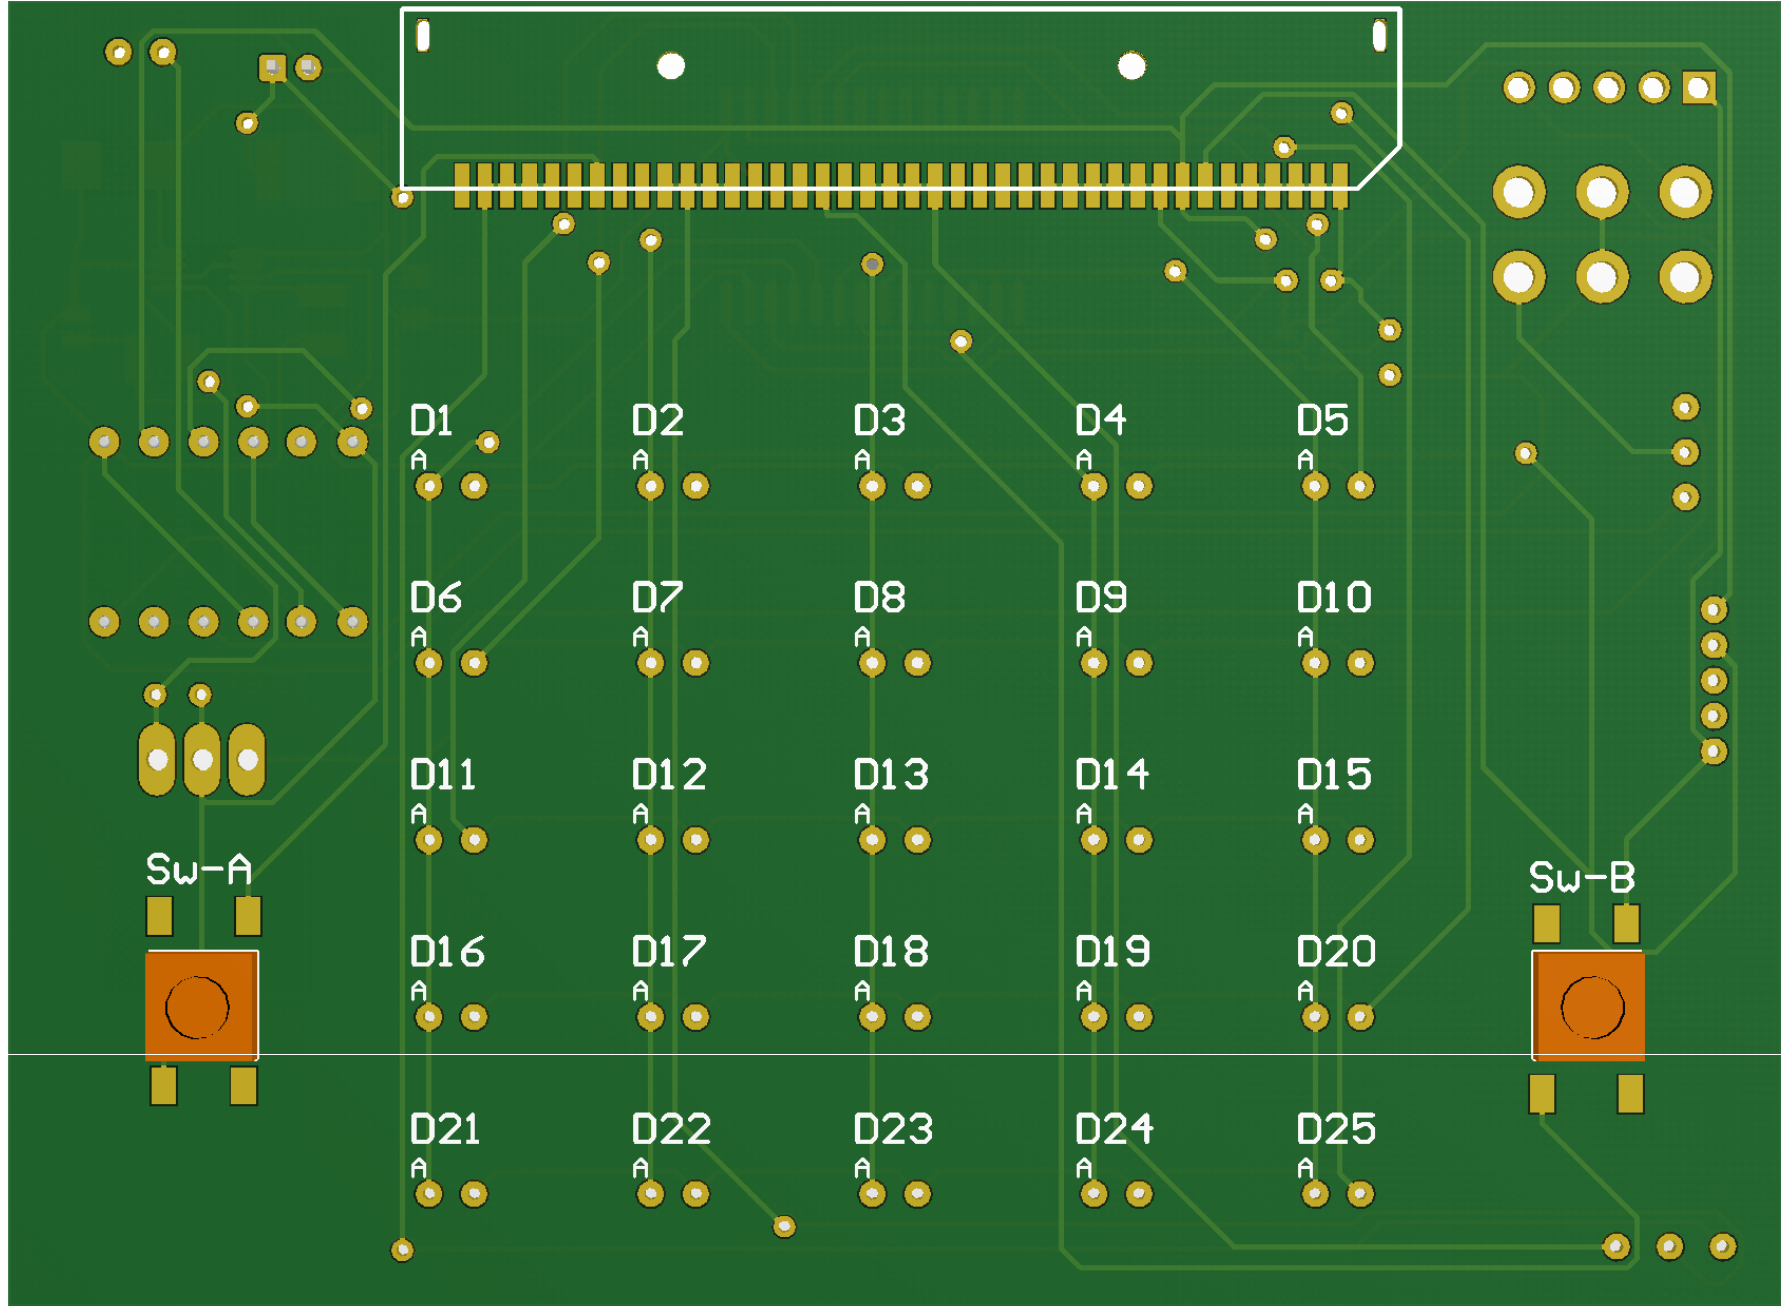
[picture p102: page 5]
