LukeB101/Mega-Bit/Design History/Hardware/PCB/PCB 1st revision/MEGABIT Rev.1.PDF

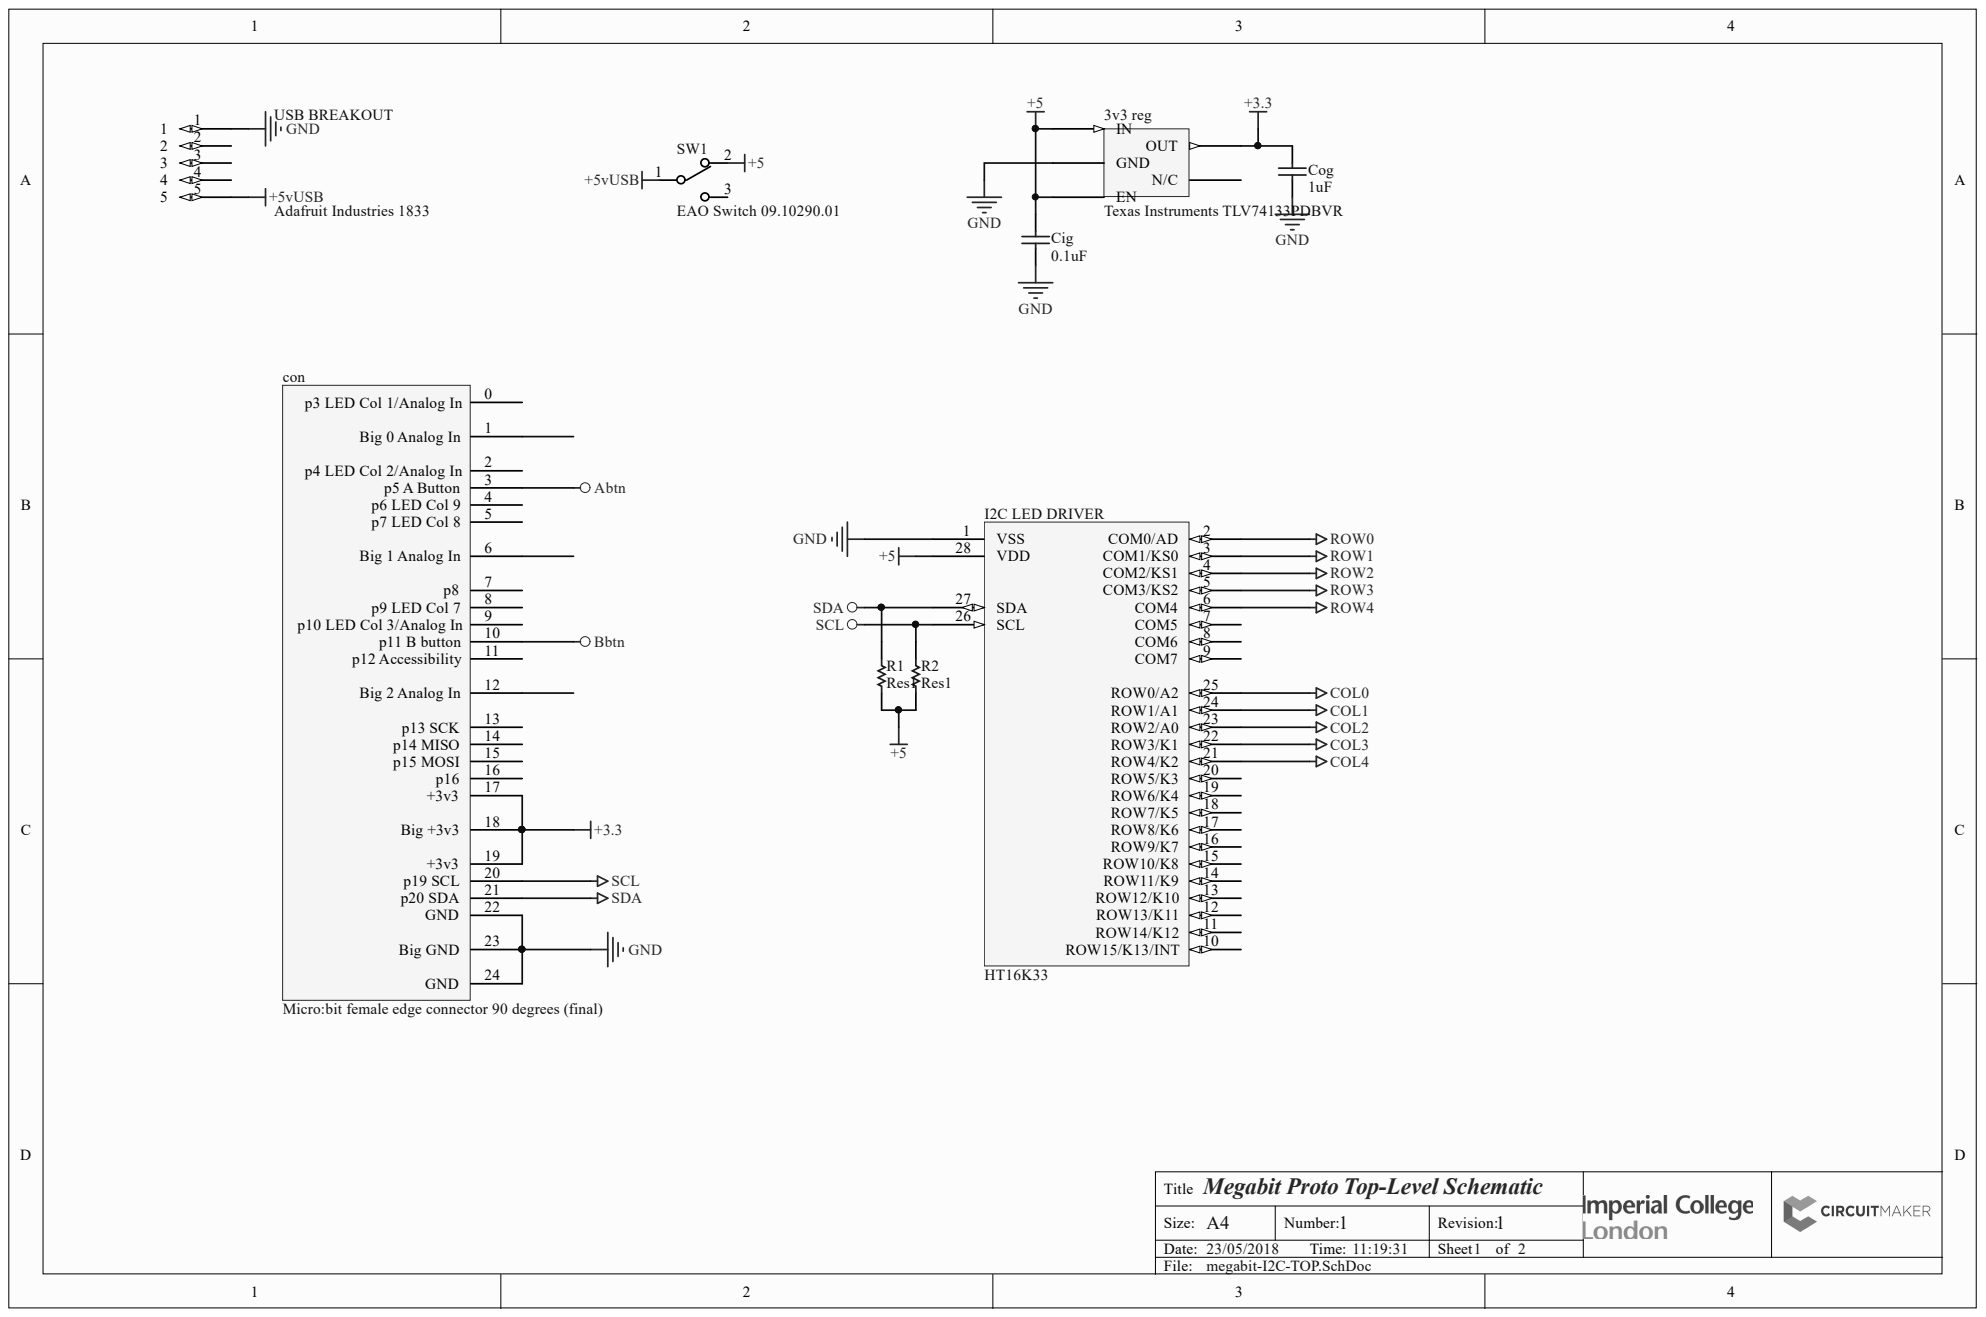
[picture p103: page 1]
VSS 1; COM0/AD; ROW15/K13/INT; 10 ROW14/K12; 11 ROW13/K11; 12 ROW12/K10; 13 ROW11/K9; 14 ROW10/K8; 15 ROW9/K7; 16 ROW8/K6; 17 ROW7/K5; 18 ROW6/K4; 19 ROW5/K3; 20 ROW4/K2; 21 ROW3/K1; 22 ROW2/A0; 23 ROW1/A1; 24 ROW0/A2; SCL 26; SDA 27; VDD 28; I2C LED DRIVER; EAO Switch 09.10290.01; USB BREAKOUT; Adafruit Industries 1833 +5vUSB; 3v3 reg; Texas Instruments TLV74133PDBVR; p3 LED Col 1/Analog In; Big 0 Analog In; p4 LED Col 2/Analog In; p5 A Button; p6 LED Col 9; p7 LED Col 8; Big 1 Analog In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

Micro:bit female edge connector 90 degrees (final)

Megabit Proto Top-Level Schematic Title

Size: A4 | Number: 1 | Revision: 1
Date: 23/05/2018 Time: 11:19:31 | | Sheet 1 of 2

megabit-I2C-TOP.SchDoc

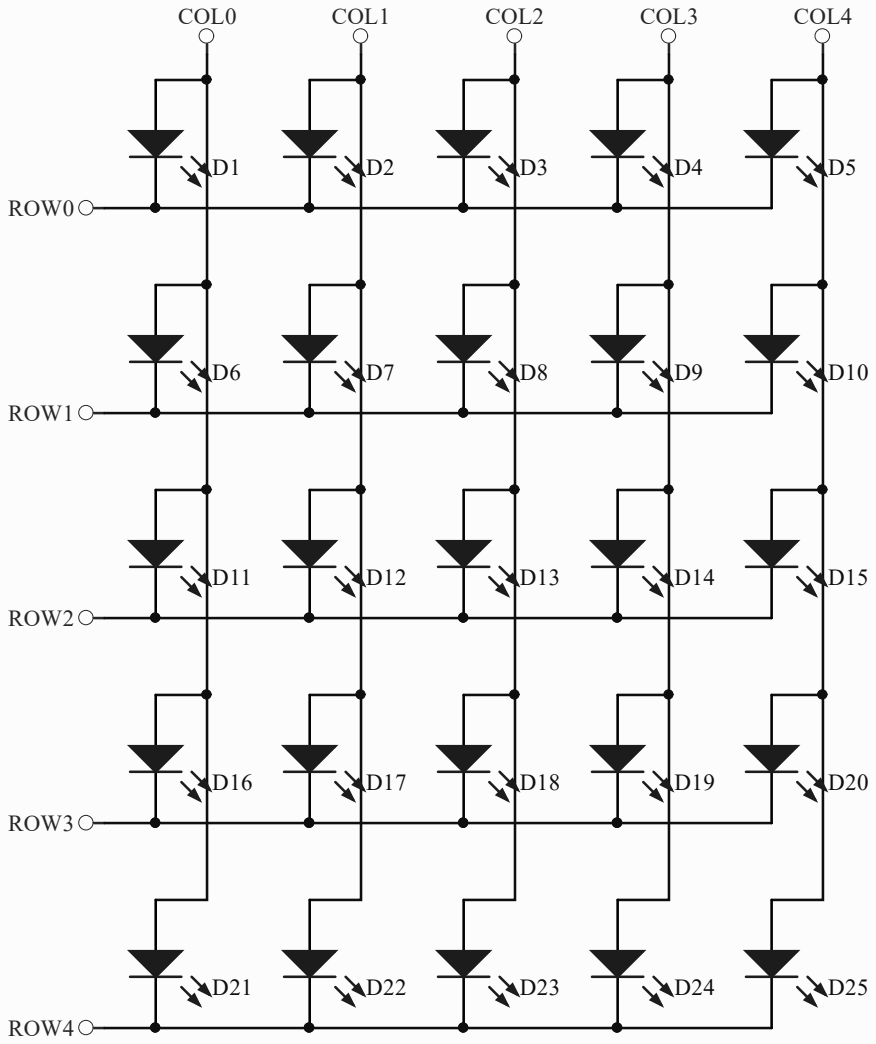
[picture p104: page 2]

Megabit LED Matrix Title

Size: A4 | Number: 1 | Revision: 1
Date: 23/05/2018 Time: 11:19:31 | | Sheet 2 of 2

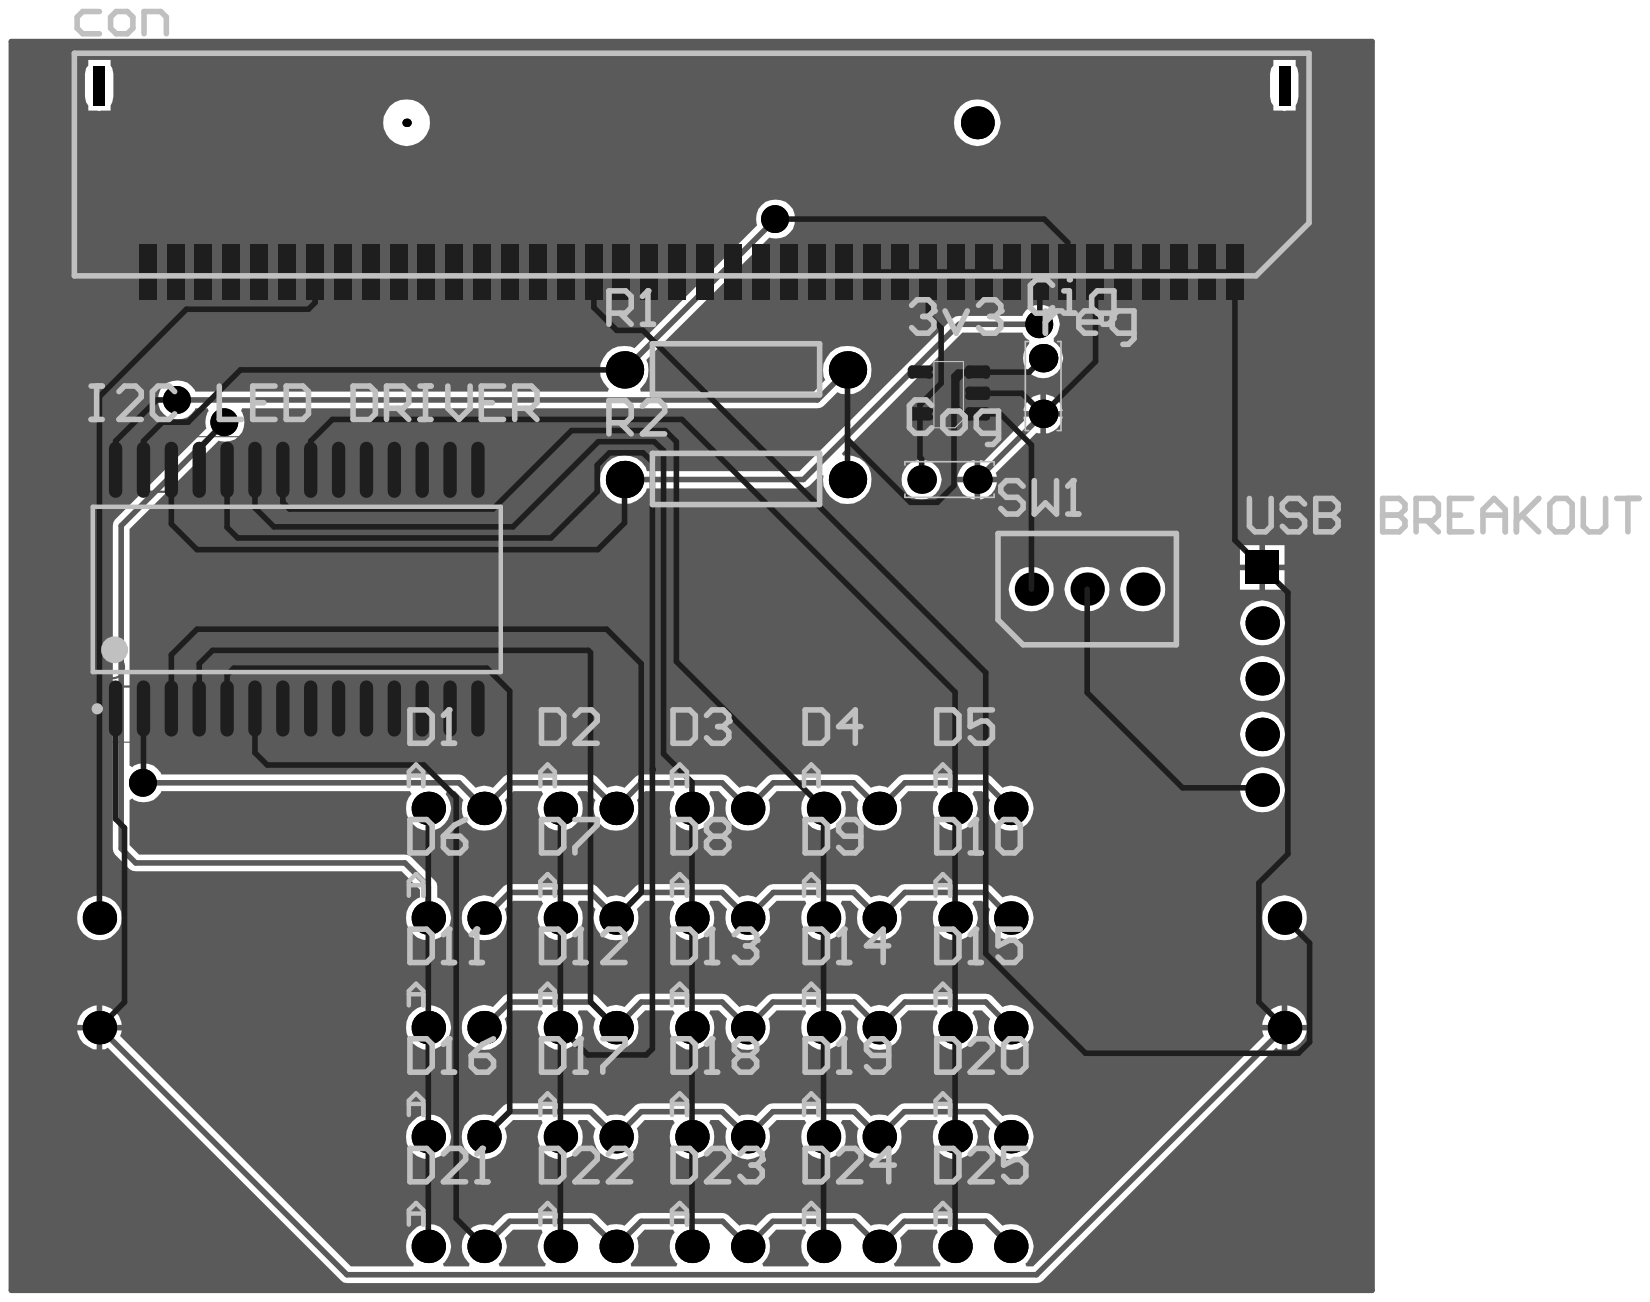
[picture p105: page 3]

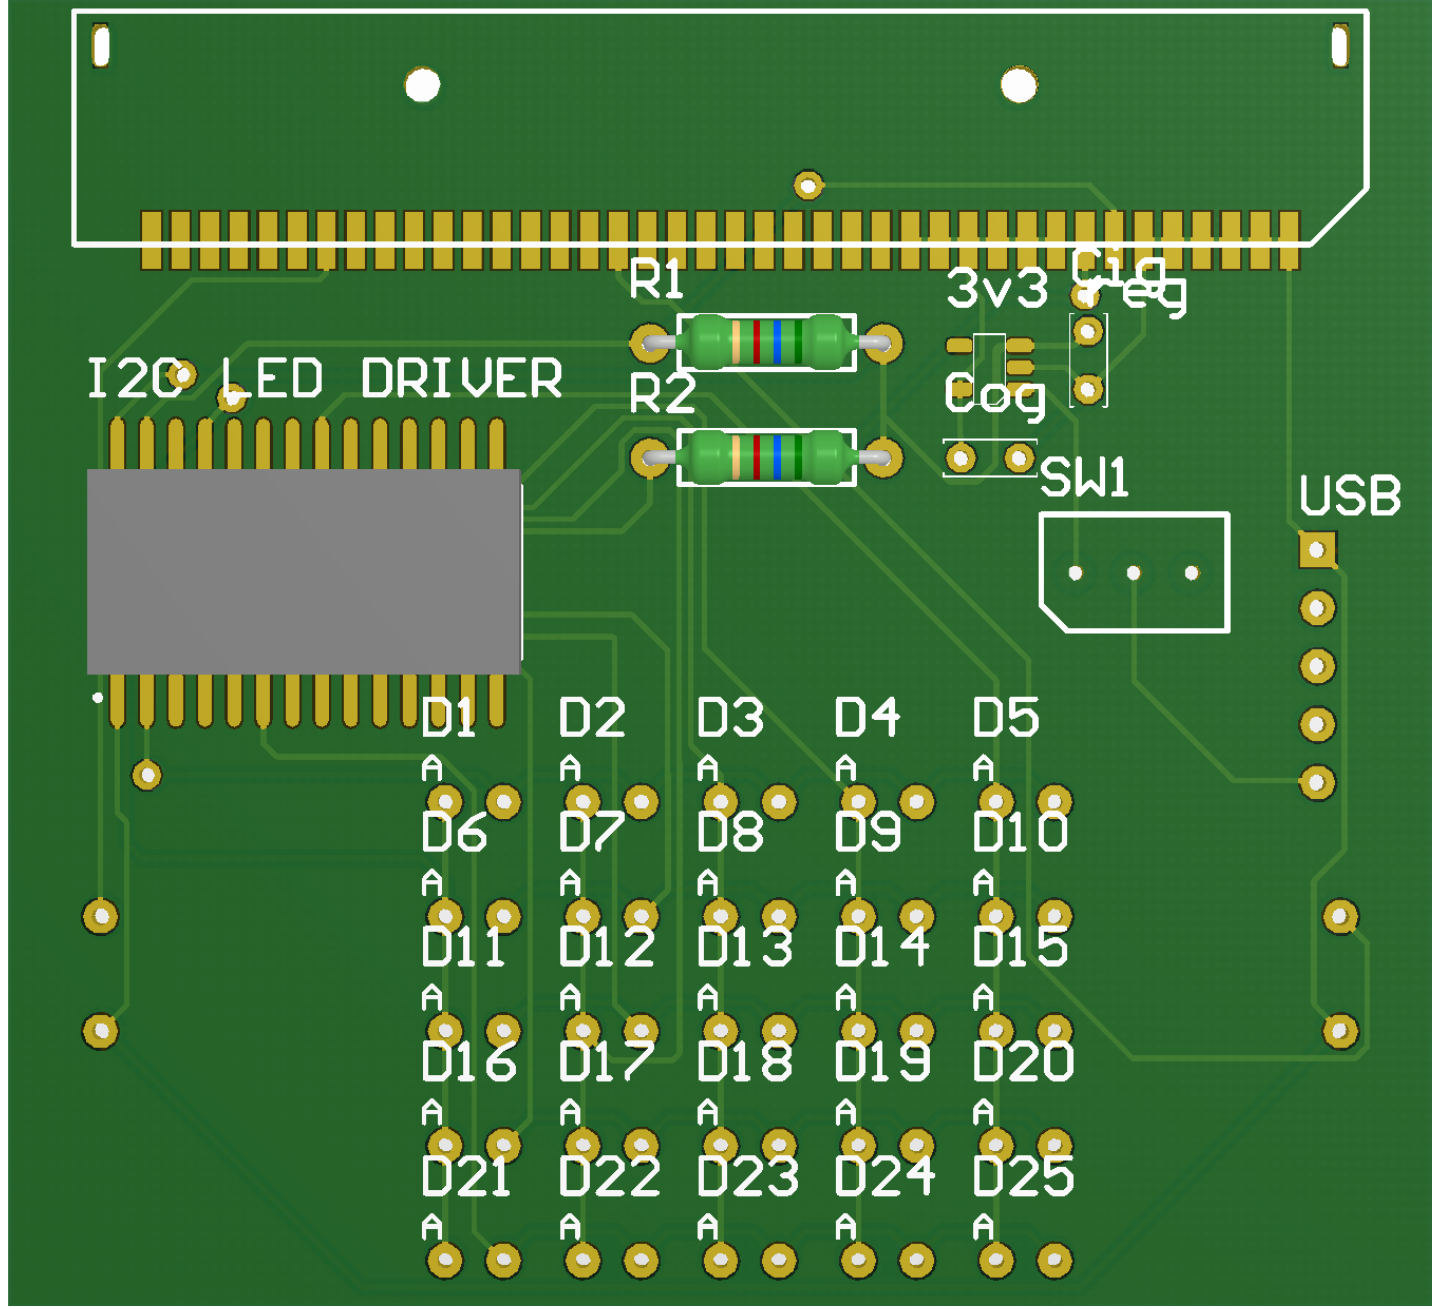
[picture p106: page 4]
