LukeB101/Mega-Bit/Design History/Components/Connector Schematics/180 degree female connector footprint.pdf

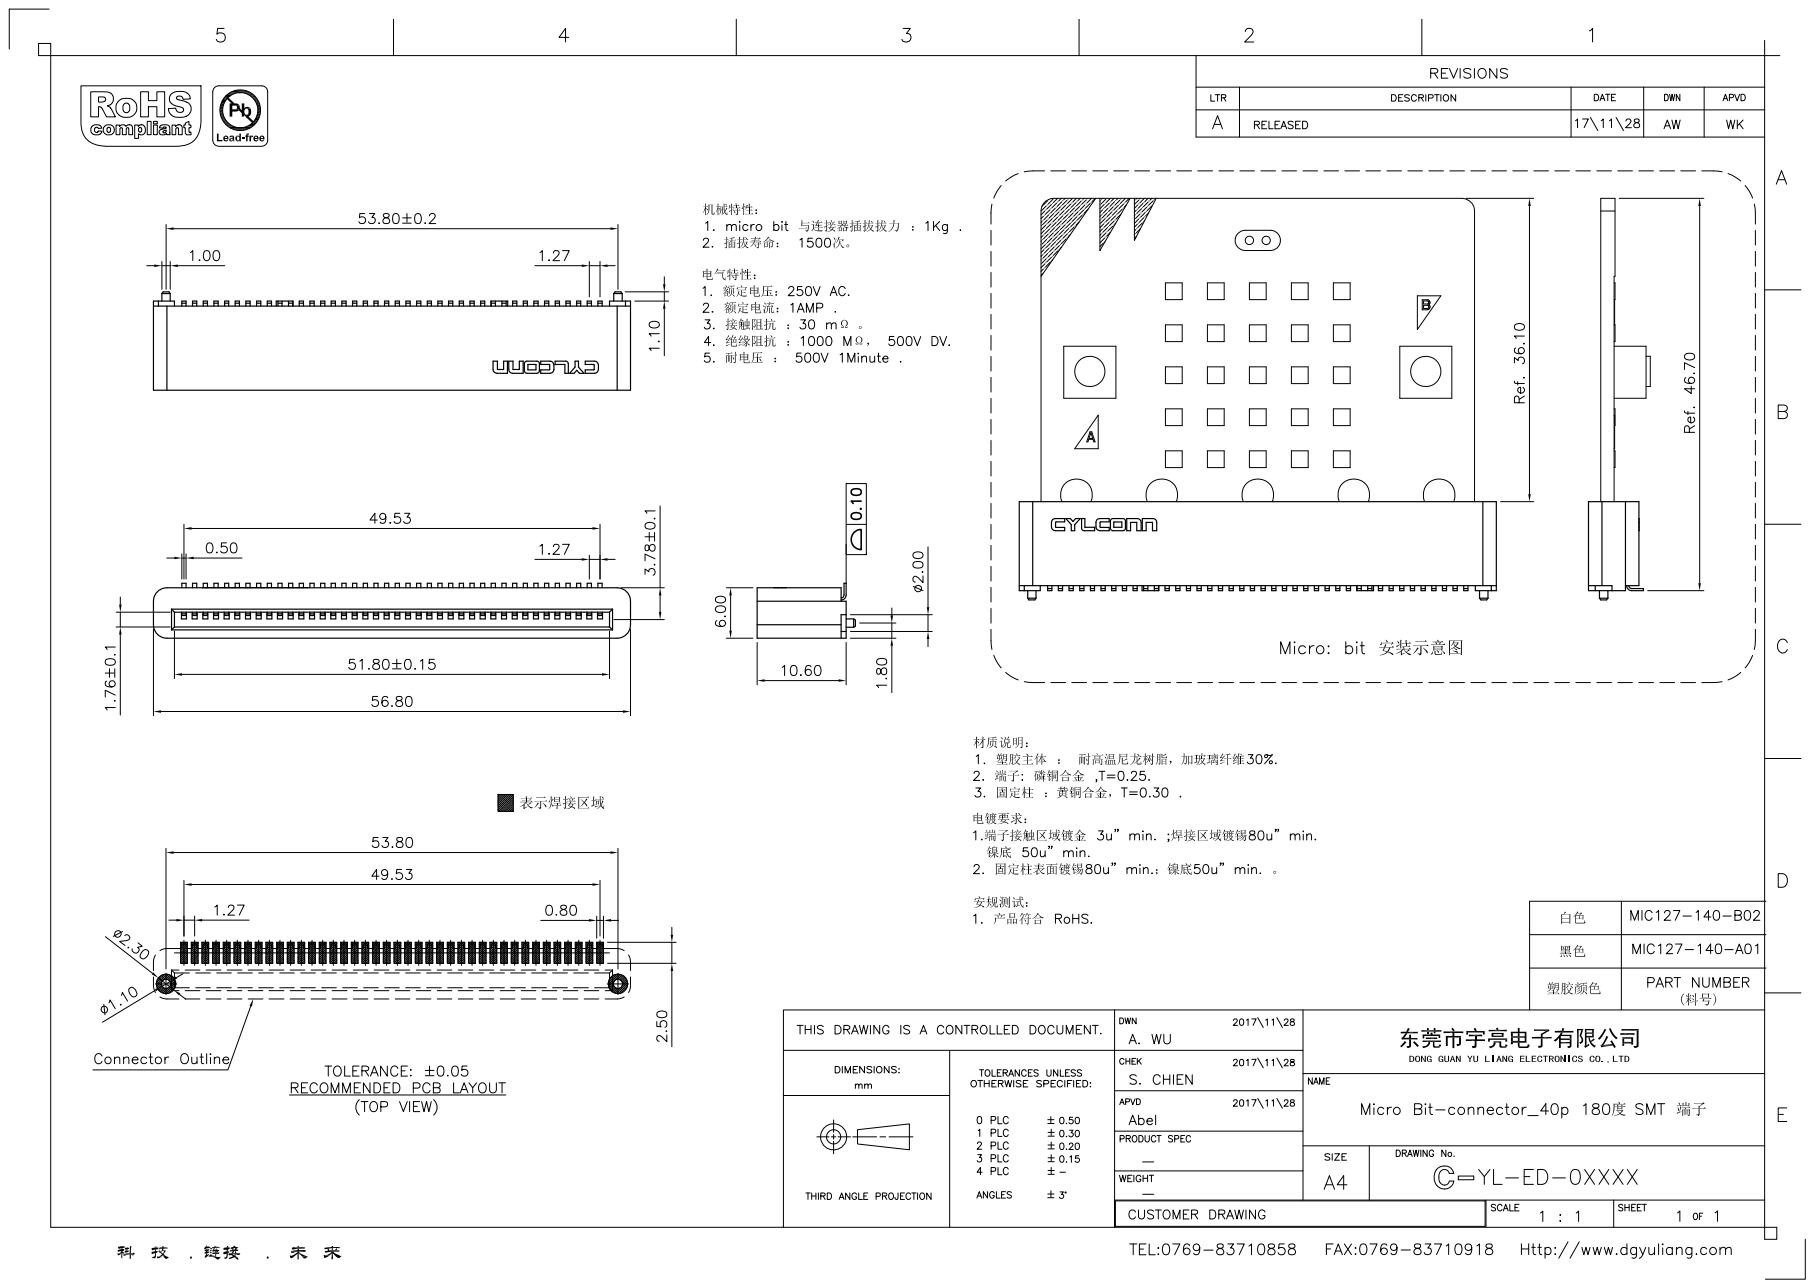
[picture p107: page 1]
