LukeB101/Mega-Bit/Design History/Components/Connector Schematics/90 degree female connector footprint (IN USE).pdf

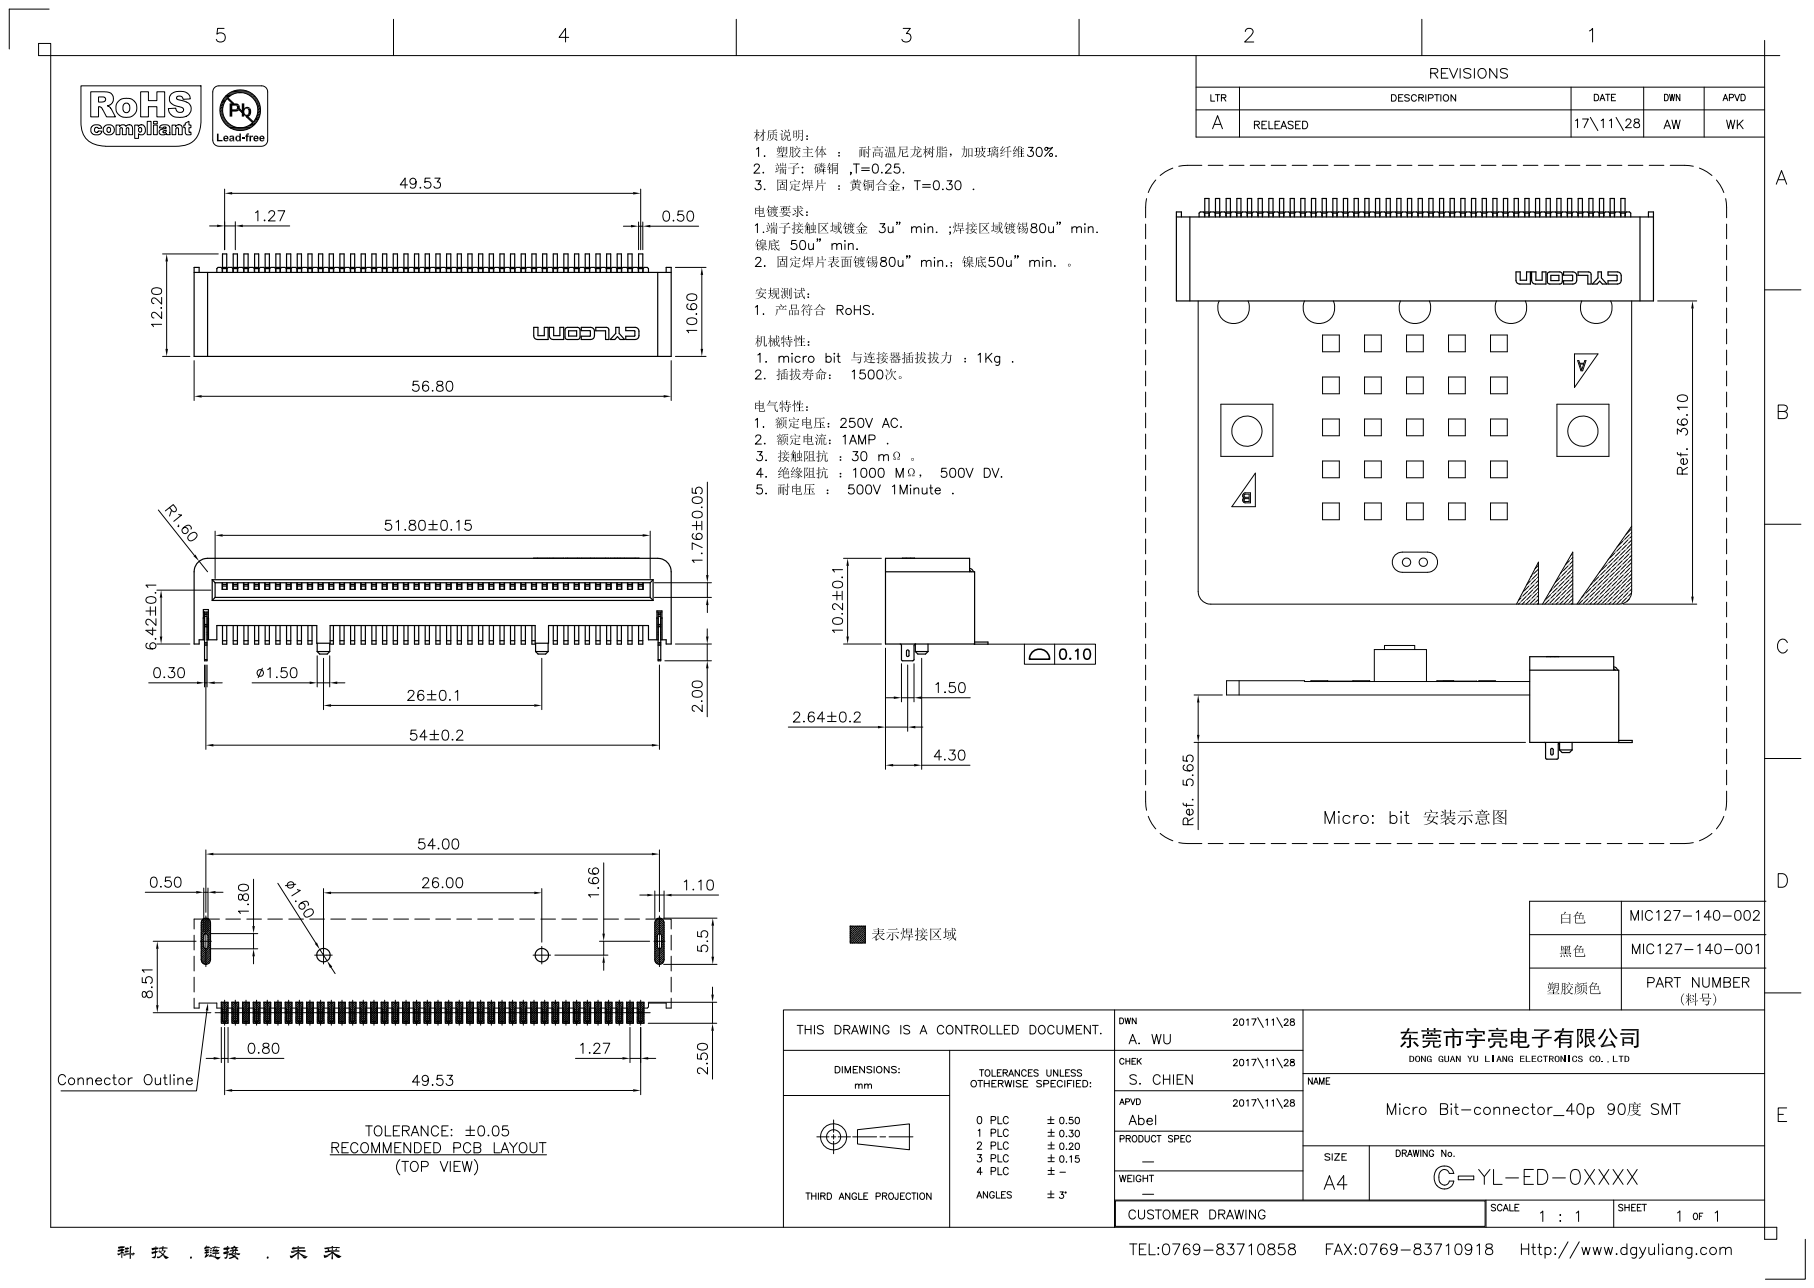
[picture p108: page 1]
