LukeB101/Mega-Bit/Design History/Components/Connector Schematics/Micro Bit-connector_40p 90.pdf

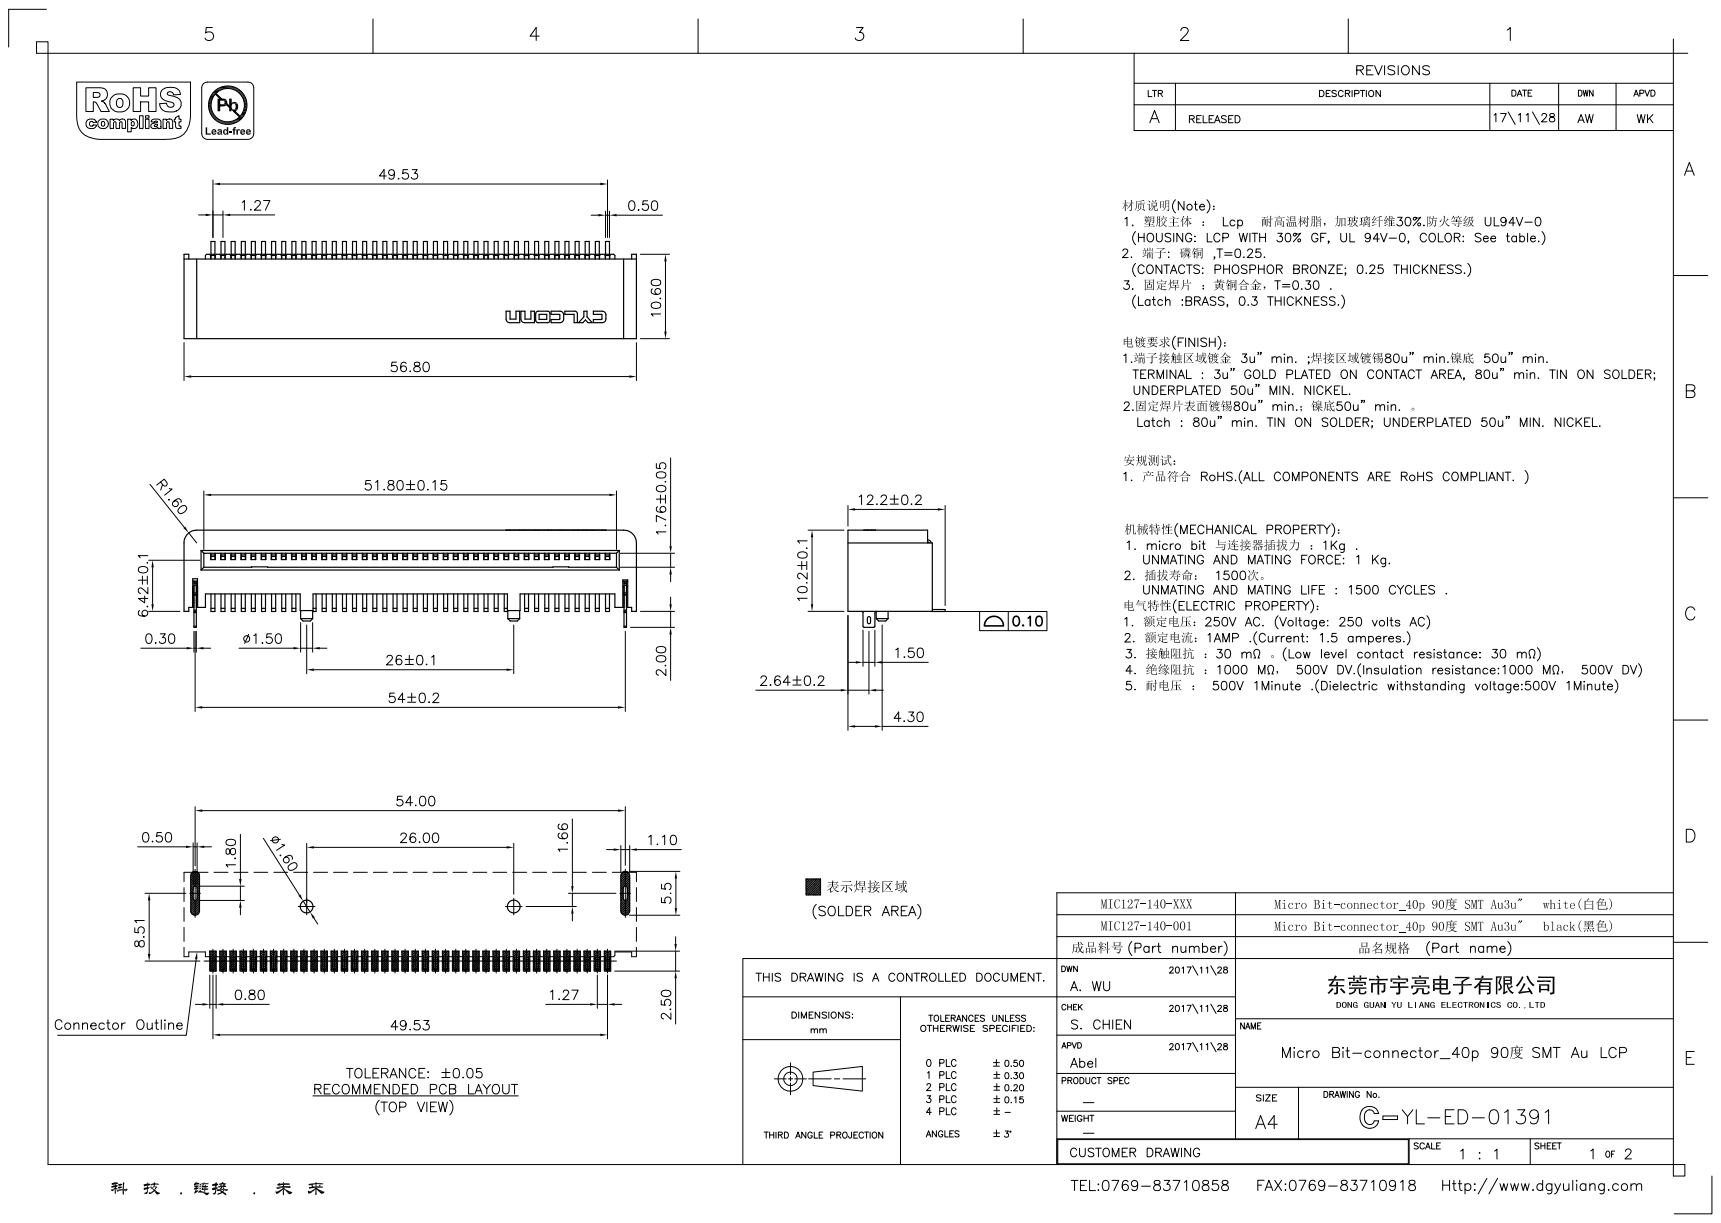
[picture p109: page 1]

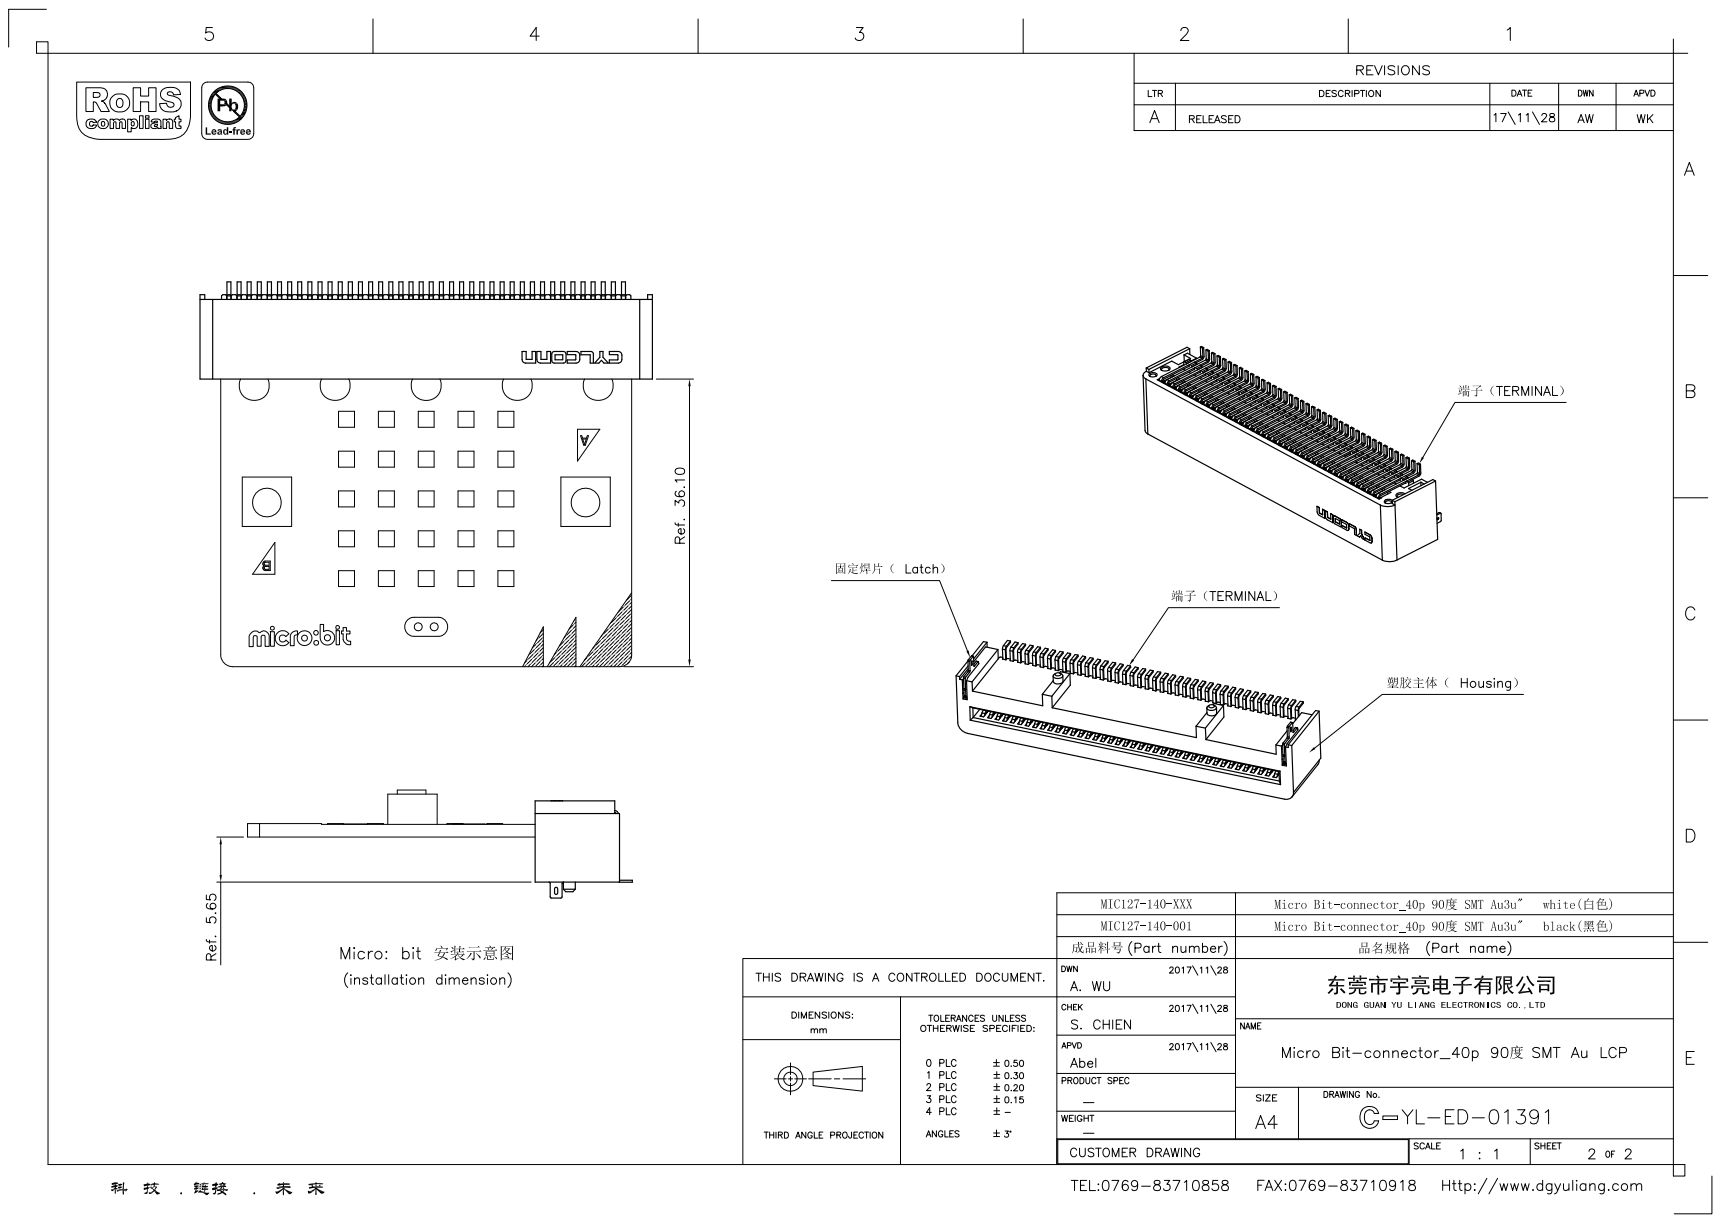
[picture p110: page 2]
